MIT-Senseable-City-Lab/flatburn-lte/documentation/content/explore/demo_usb_data.gif

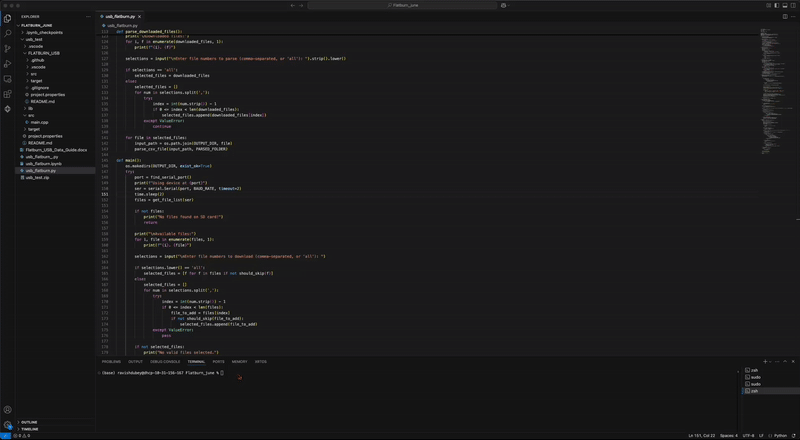
documentation/content/explore/demo_usb_data.gif
