MIT-Senseable-City-Lab/flatburn-lte/hardware/enclosure/step/mechanics/3d_printing/switch radial - R10307RN02Q/MP-05 switch_bottom.stp

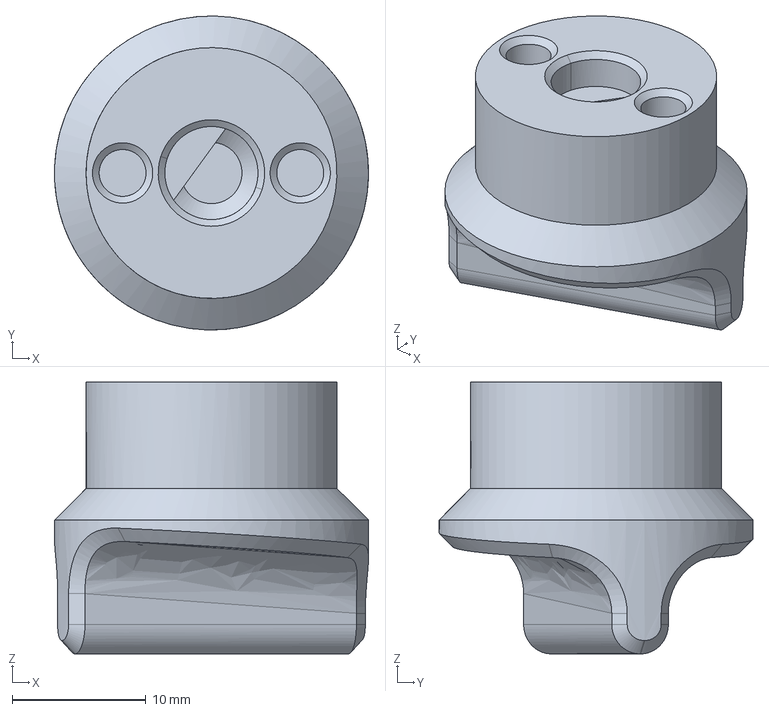
[picture p43: CAD file, 2025-01-15]
hardware/enclosure/step/mechanics/3d_printing/switch radial - R10307RN02Q/MP-05 switch_bottom.stp
23.4 x 23.4 x 20.3 mm
