MIT-Senseable-City-Lab/flatburn-lte/hardware/enclosure/step/mechanics/sealing/MS-02 oring_cord.stp

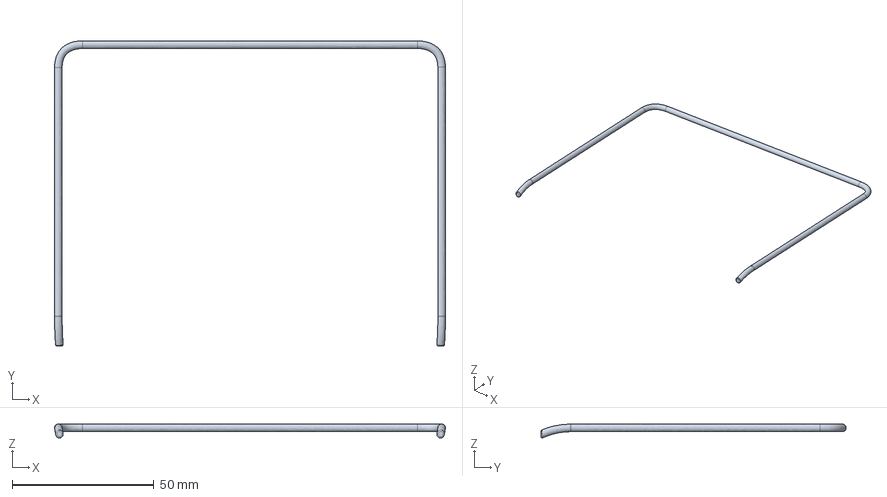
[picture p44: CAD file, 2025-01-15]
hardware/enclosure/step/mechanics/sealing/MS-02 oring_cord.stp
137.8 x 107.6 x 4.94 mm
