MIT-Senseable-City-Lab/flatburn-lte/hardware/enclosure/stl/MP-06 battery_cover.stl

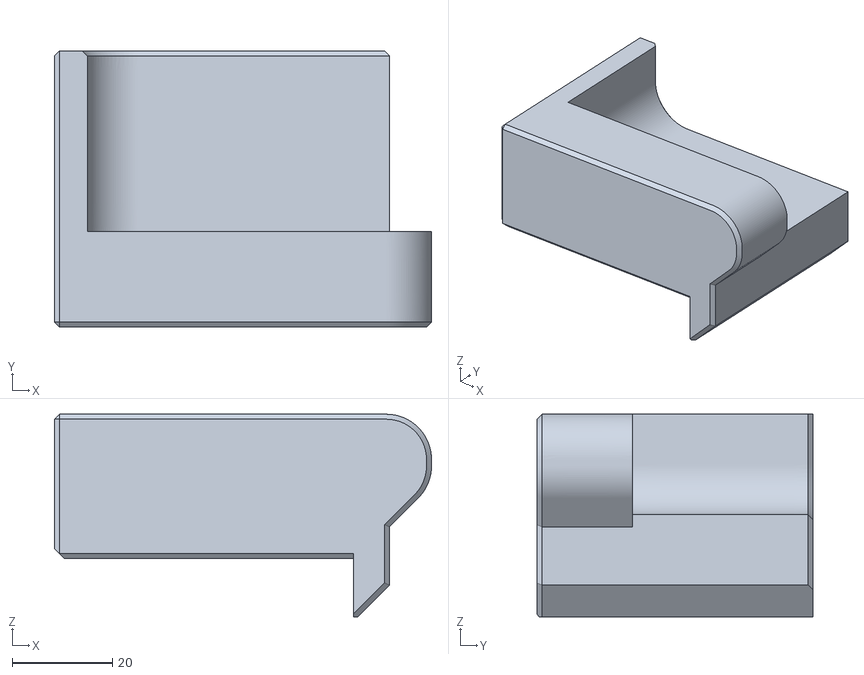
[picture p45: CAD file, 2025-01-15]
hardware/enclosure/stl/MP-06 battery_cover.stl
75.1 x 55.0 x 40.3
