MIT-Senseable-City-Lab/flatburn-lte/hardware/enclosure/bambu/switch_linear_SLW-135987-5A-N-D.3mf

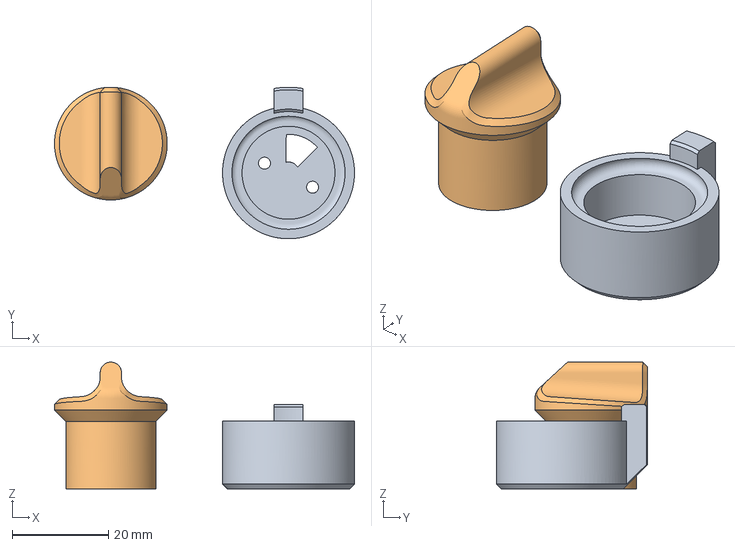
[picture p46: CAD file, 2025-01-20]
hardware/enclosure/bambu/switch_linear_SLW-135987-5A-N-D.3mf
62.4 x 31.5 x 26.4 mm
MP-04 switch_top.stl
MP-05 switch_bottom.stl
