MIT-Senseable-City-Lab/flatburn-lte/hardware/enclosure/step/electronics/switch linear - SLW-135987-5A-N-D.stp

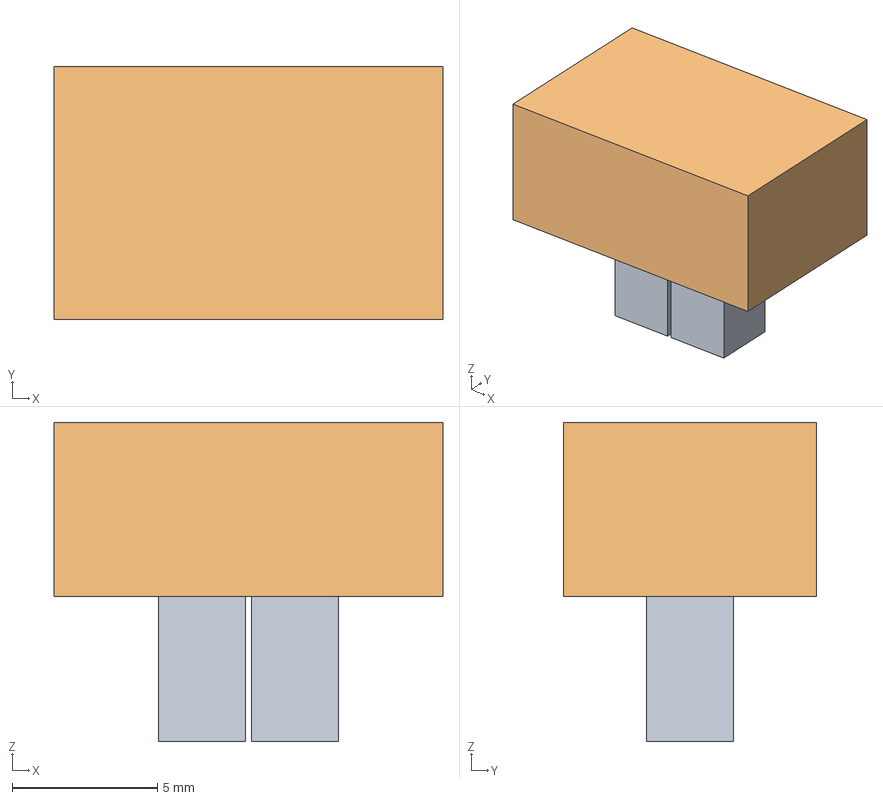
[picture p47: CAD file, 2025-01-16]
hardware/enclosure/step/electronics/switch linear - SLW-135987-5A-N-D.stp
13.4 x 8.70 x 11.0 mm
