MIT-Senseable-City-Lab/flatburn-lte/hardware/enclosure/step/mechanics/fixation/MF-07 spacer_6mm.stp

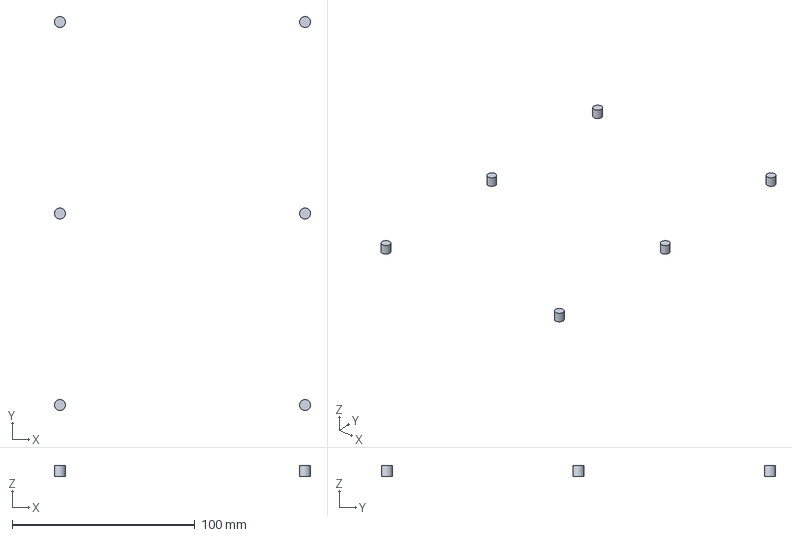
[picture p48: CAD file, 2025-01-15]
hardware/enclosure/step/mechanics/fixation/MF-07 spacer_6mm.stp
140.0 x 215.4 x 6.00 mm
