MIT-Senseable-City-Lab/flatburn-lte/hardware/enclosure/step/electronics/switch linear - FS22AXX.stp

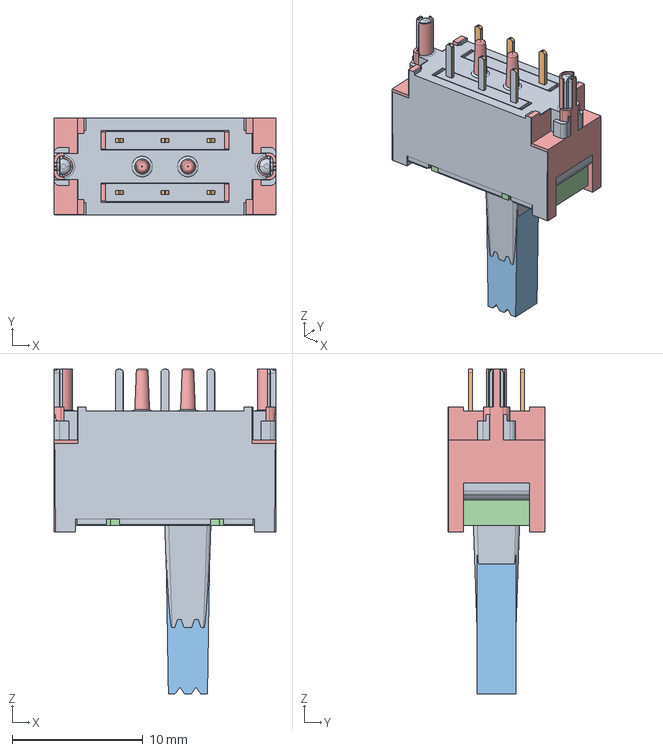
[picture p49: CAD file, 2025-01-16]
hardware/enclosure/step/electronics/switch linear - FS22AXX.stp
17.0 x 7.40 x 24.9 mm
