MIT-Senseable-City-Lab/flatburn-lte/hardware/enclosure/step/mechanics/fixation/MF-02 insert_m2.stp

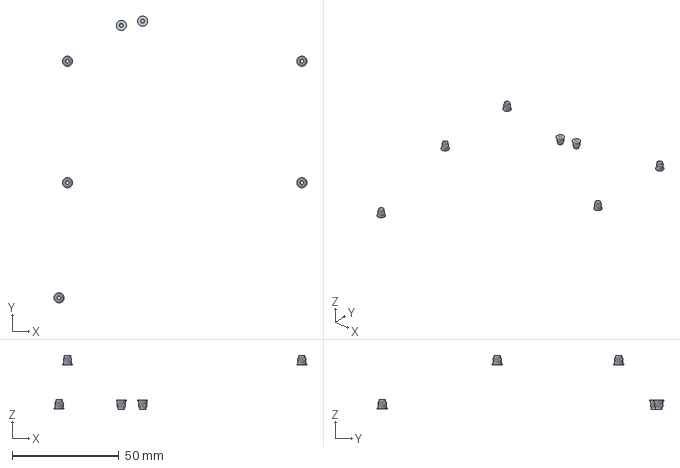
[picture p50: CAD file, 2025-01-15]
hardware/enclosure/step/mechanics/fixation/MF-02 insert_m2.stp
118.7 x 134.6 x 25.5 mm
