MIT-Senseable-City-Lab/flatburn-lte/hardware/enclosure/step/electronics/ES-01 sensor_gas.stp

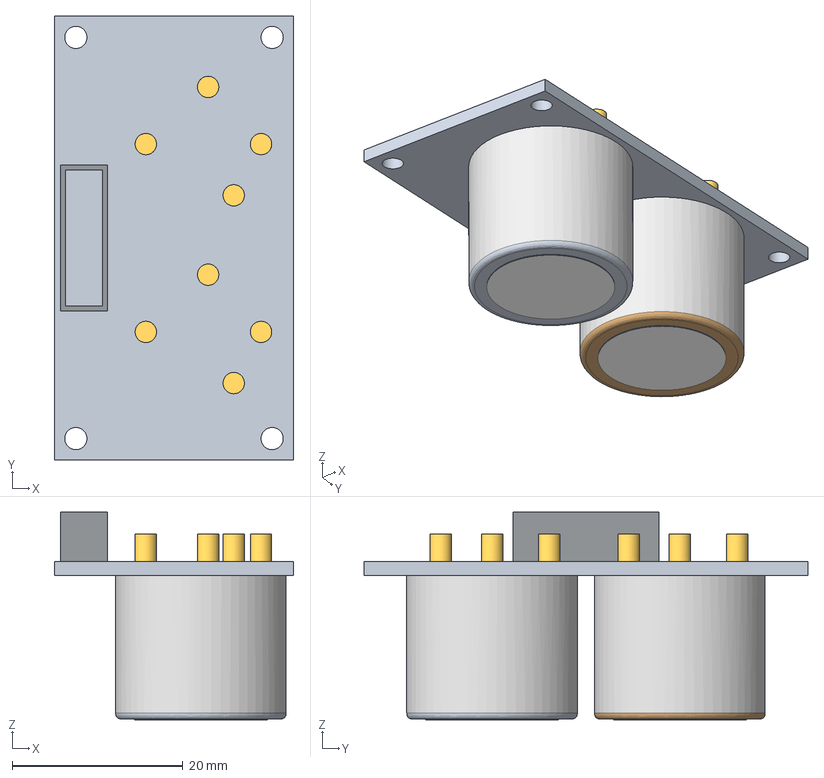
[picture p51: CAD file, 2025-01-15]
hardware/enclosure/step/electronics/ES-01 sensor_gas.stp
28.0 x 52.0 x 24.3 mm
