MIT-Senseable-City-Lab/flatburn-lte/hardware/enclosure/step/electronics/EH-03 90deg_adapter_usb.stp

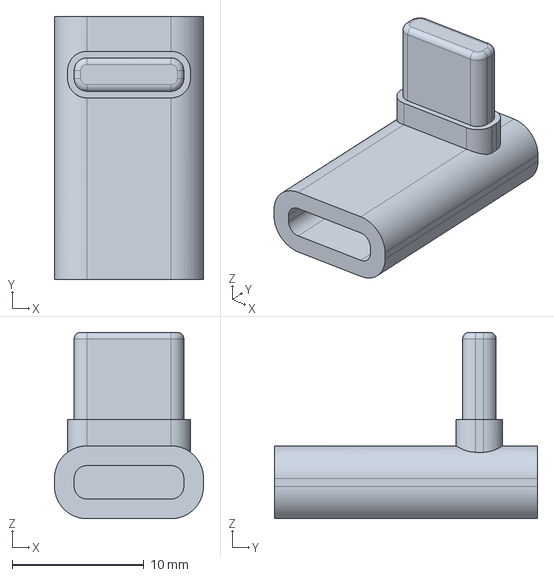
[picture p52: CAD file, 2025-01-15]
hardware/enclosure/step/electronics/EH-03 90deg_adapter_usb.stp
11.3 x 20.0 x 14.2 mm
