MIT-Senseable-City-Lab/flatburn-lte/hardware/enclosure/bambu/switch_linear_FS22AXX.3mf

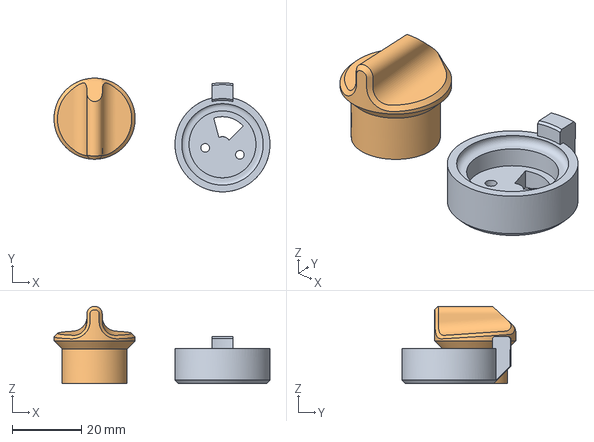
[picture p53: CAD file, 2025-01-15]
hardware/enclosure/bambu/switch_linear_FS22AXX.3mf
62.4 x 32.9 x 22.4 mm
MP-04 switch_top.stl
MP-05 switch_bottom.stl
