MIT-Senseable-City-Lab/flatburn-lte/hardware/enclosure/step/electronics/EP-02 solar_panel.stp

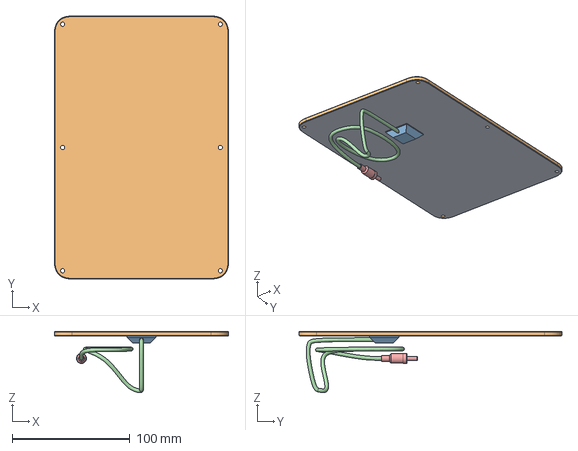
[picture p54: CAD file, 2025-01-15]
hardware/enclosure/step/electronics/EP-02 solar_panel.stp
148.0 x 223.4 x 52.0 mm
