MIT-Senseable-City-Lab/flatburn-lte/hardware/enclosure/step/electronics/EV-01 micro_sd.stp

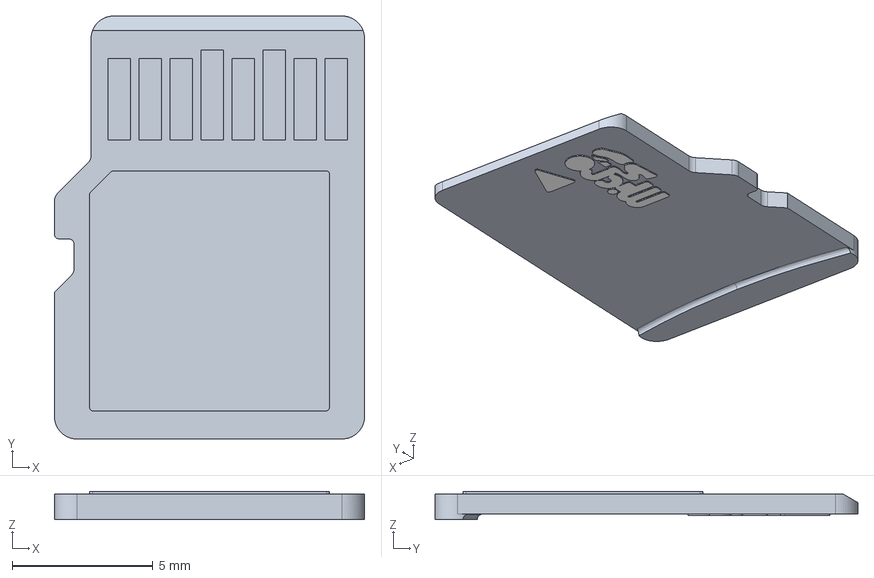
[picture p55: CAD file, 2025-01-15]
hardware/enclosure/step/electronics/EV-01 micro_sd.stp
11.0 x 15.0 x 1.00 mm
