MIT-Senseable-City-Lab/flatburn-lte/hardware/enclosure/step/electronics/ES-02 sensor_particulate.stp

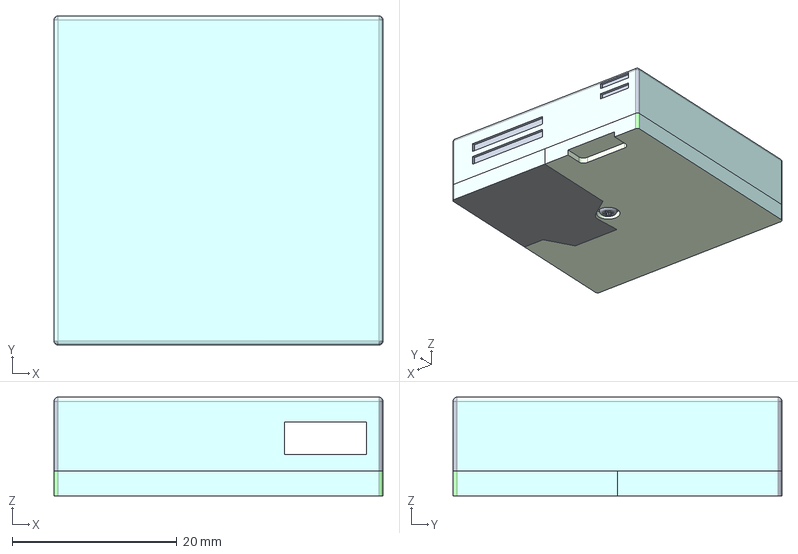
[picture p56: CAD file, 2025-01-15]
hardware/enclosure/step/electronics/ES-02 sensor_particulate.stp
40.0 x 40.0 x 12.0 mm
