MIT-Senseable-City-Lab/flatburn-lte/hardware/enclosure/step/electronics/EP-01 battery.stp

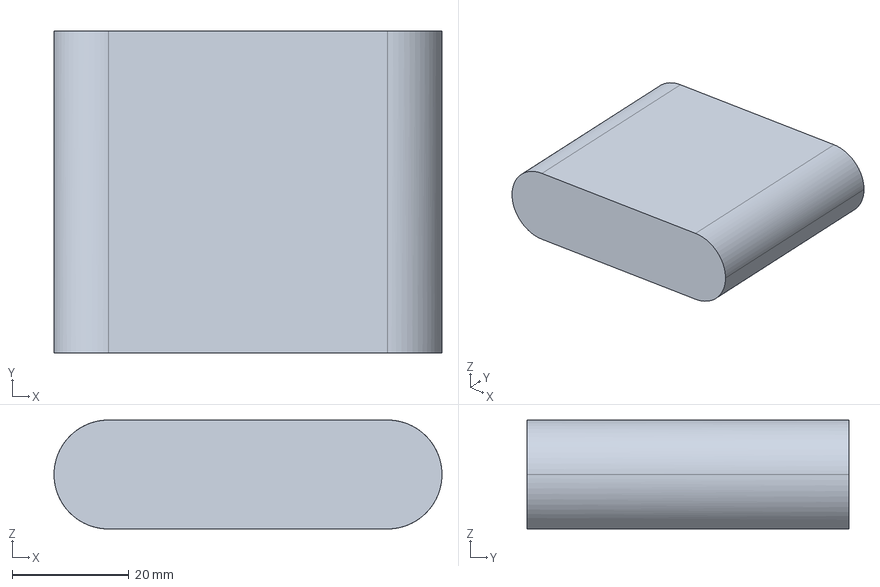
[picture p57: CAD file, 2025-01-15]
hardware/enclosure/step/electronics/EP-01 battery.stp
66.6 x 55.3 x 18.7 mm
