MIT-Senseable-City-Lab/flatburn-lte/hardware/enclosure/step/electronics/EH-04 waterproof_usb.stp

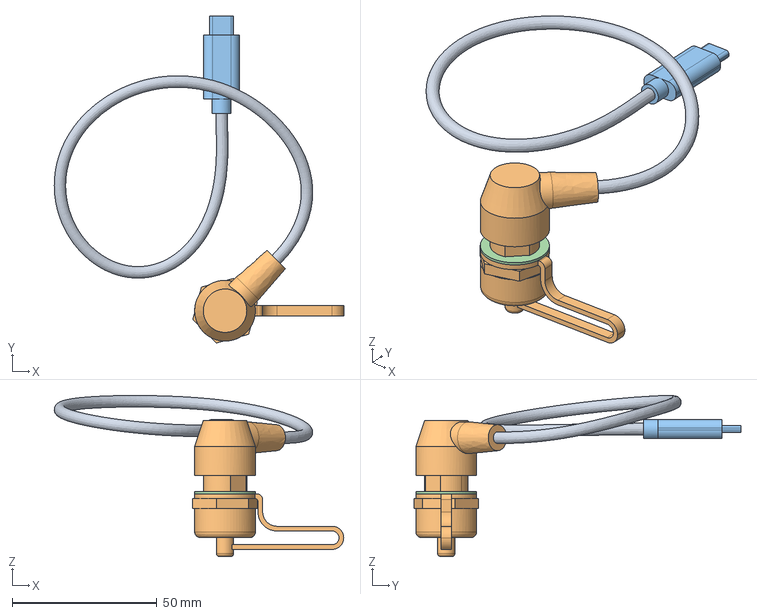
[picture p58: CAD file, 2025-01-15]
hardware/enclosure/step/electronics/EH-04 waterproof_usb.stp
100.0 x 112.9 x 55.6 mm
