MIT-Senseable-City-Lab/flatburn-lte/hardware/electronics/Flatburn_V5.kicad_sch

## KiCad design hardware/electronics/Flatburn_V5.kicad_sch (2025-08-07)

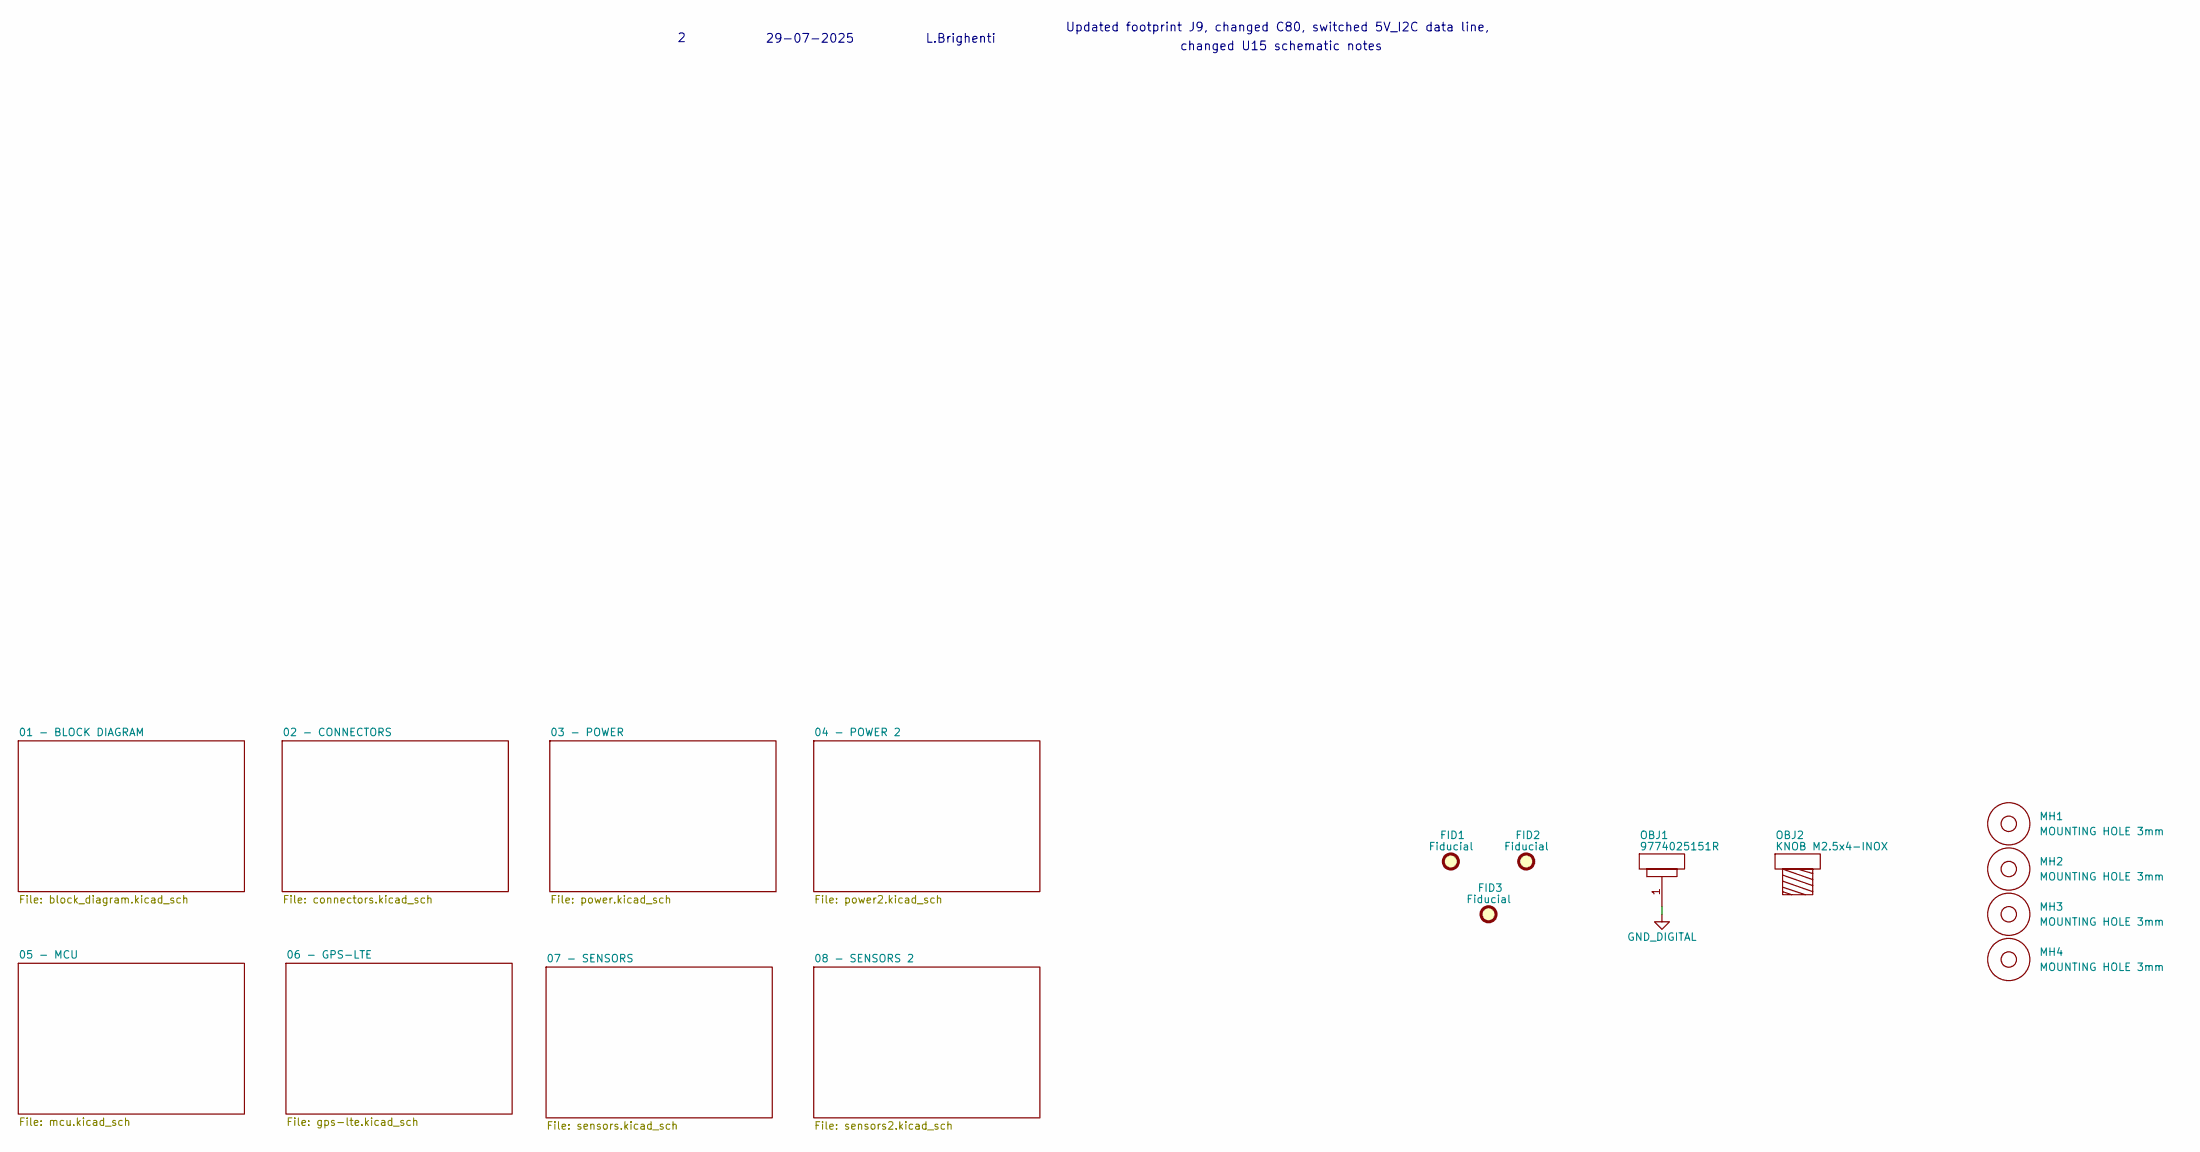
[picture p169: schematic Flatburn_V5.kicad_sch]

Parts:
FID1, FID2, FID3: Fiducial; Fiducial_1mm_Mask3mm
MH1, MH2, MH3, MH4: MOUNTING HOLE 3mm
OBJ1: 9774025151R; SPACER M2.5 - 9774025151R; MPN 9774025151R
OBJ2: KNOB M2.5x4-INOX

Connections:
GND_DIGITAL: OBJ1.1

Notes on the sheet:
L.Brighenti
Updated footprint J9, changed C80, switched 5V_I2C data line,
29-07-2025
changed U15 schematic notes
