MIT-Senseable-City-Lab/flatburn-lte/hardware/electronics/connectors.kicad_sch

## KiCad design hardware/electronics/connectors.kicad_sch (2025-08-07)

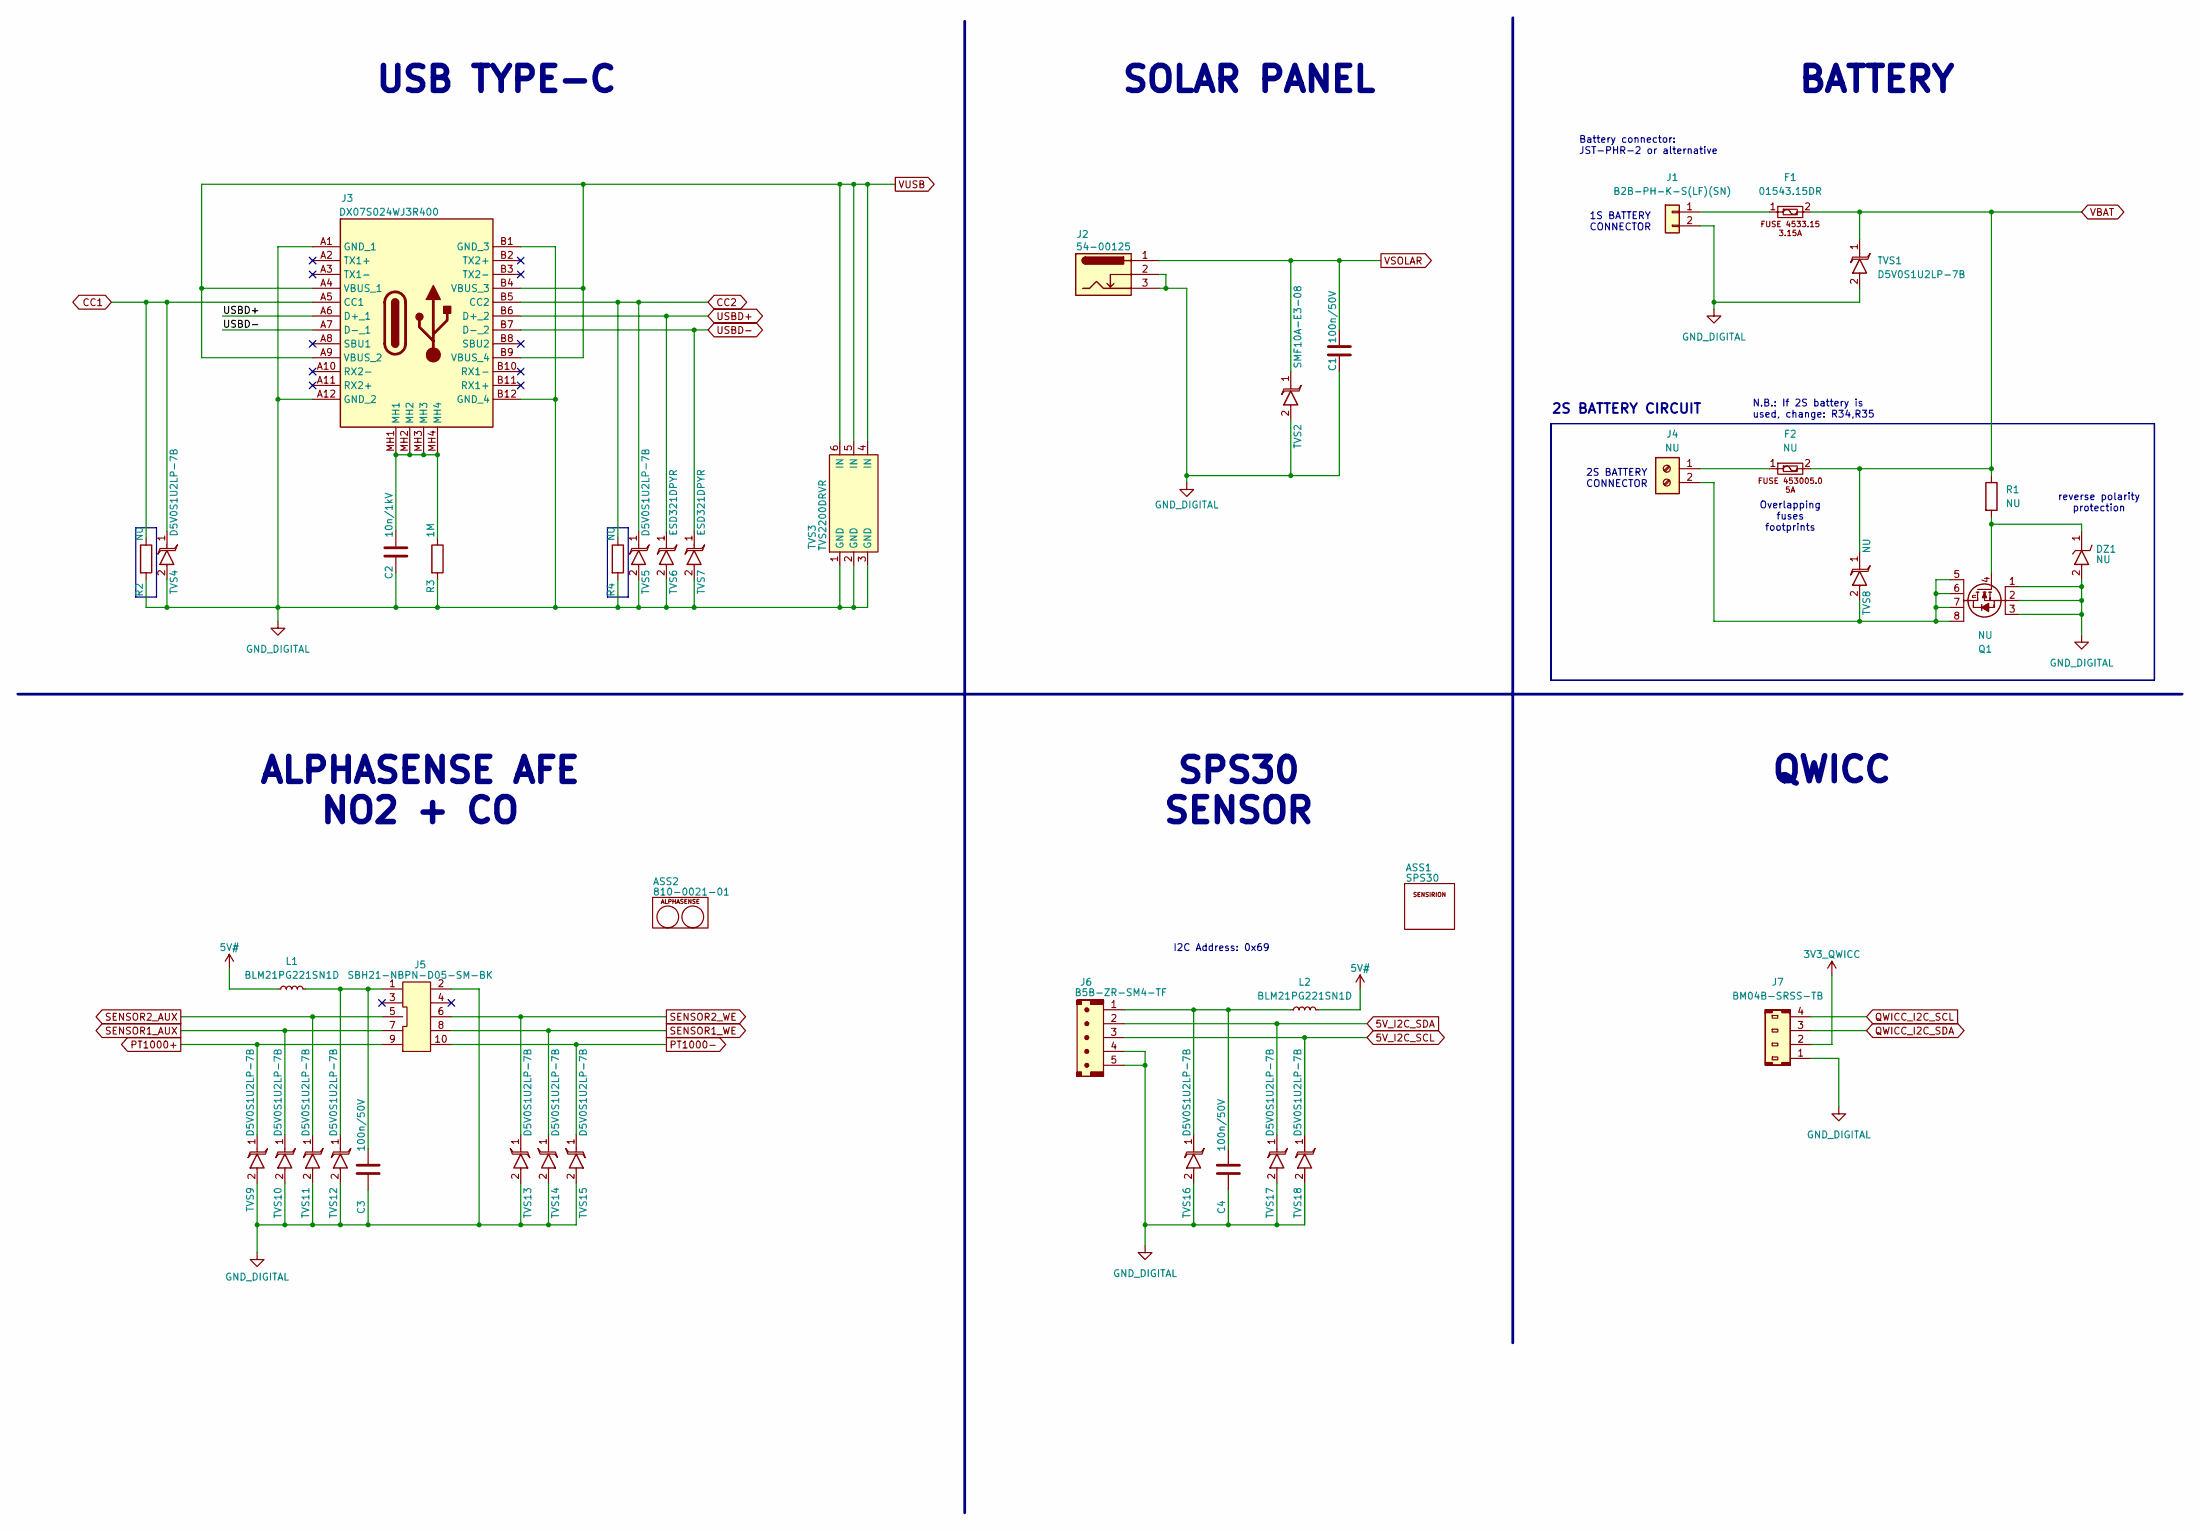
[picture p170: schematic connectors.kicad_sch]

Parts:
ASS1: SPS30; MPN SPS30
ASS2: 810-0021-01; MPN 810-0021-01
C1, C3, C4: 100n/50V; C_0402_1005Metric
C2: 10n/1kV; C_1206_3216Metric
DZ1: NU; D_SOD-523; MPN BZT52C12T-7
F1: 01543.15DR; 154SERIES; MPN 01543.15DR
F2: NU; 154SERIES; MPN 0154005.DR
J1: B2B-PH-K-S(LF)(SN); JST_PH_B2B-PH-K_1x02_P2.00mm_Vertical; MPN B2B-PH-K-S(LF)(SN)
J2: 54-00125; MPN 54-00125
J3: DX07S024WJ3R400; MPN DX07S024WJ3R400
J4: NU; 39543-4302; MPN 39543-4302
J5: SBH21-NBPN-D05-SM-BK; MPN SBH21-NBPN-D05-SM-BK
J6: B5B-ZR-SM4-TF; MPN B5B-ZR-SM4-TF
J7: BM04B-SRSS-TB; BM04B-SRSS_JST; MPN BM04B-SRSS-TB
L1, L2: BLM21PG221SN1D; L_0805_2012Metric; MPN BLM21PG221SN1D
Q1: NU; PowerPAK 121-8; MPN SISH402DN-T1-GE3
R1: NU; R_0402_1005Metric
R2, R4: NU; R_0603_1608Metric; MPN RC0603FR-105K1L
R3: 1M; R_1206_3216Metric
TVS1, TVS4, TVS5, TVS9, TVS10, TVS11, TVS12, TVS13, TVS14, TVS15, TVS16, TVS17, TVS18: D5V0S1U2LP-7B; D5V0S1U2LP7B; MPN M-621-D5V0S1U2LP-7B
TVS2: SMF10A-E3-08; D_SMF; MPN SMF10A-E3-08
TVS3: TVS2200DRVR; SON65P200X200X80-7N; MPN TVS2200DRVR
TVS6, TVS7: ESD321DPYR; X1SON-2; MPN ESD321DPYR
TVS8: NU; D_SMF; MPN SMF10A-E3-08

Connections:
3V3_QWICC: J7.2
5V#: L1.2, L2.1
5V_I2C_SCL: J6.3, TVS18.1
5V_I2C_SDA: J6.2, TVS17.1
CC1: J3.A5 (CC1), R2.1, TVS4.1
CC2: J3.B5 (CC2), R4.1, TVS5.1
GND_DIGITAL: C1.2, C2.2, C3.2, C4.2, DZ1.2, J1.2, J2.2, J2.3, J3.A1 (GND_1), J3.A12 (GND_2), J3.B1 (GND_3), J3.B12 (GND_4), J5.2, J6.4, J6.5, J7.1, Q1.1 (S), Q1.2 (S), Q1.3 (S), R2.2, R3.2, R4.2, TVS1.2, TVS2.2, TVS3.1 (GND), TVS3.2 (GND), TVS3.3 (GND), TVS3.7 (GND), TVS4.2, TVS5.2, TVS6.2, TVS7.2, TVS9.2, TVS10.2, TVS11.2, TVS12.2, TVS13.2, TVS14.2, TVS15.2, TVS16.2, TVS17.2, TVS18.2
unnamed: C2.1, J3.MH1, J3.MH2, J3.MH3, J3.MH4, R3.1
unnamed: C3.1, J5.1, L1.1, TVS12.1
unnamed: C4.1, J6.1, L2.2, TVS16.1
unnamed: DZ1.1, Q1.4 (G), R1.2
unnamed: F1.1, J1.1
unnamed: F2.1, J4.1
unnamed: J4.2, Q1.5 (D), Q1.6 (D), Q1.7 (D), Q1.8 (D), Q1.9 (D), TVS8.2
PT1000+: J5.9, TVS9.1
PT1000-: J5.10, TVS15.1
QWICC_I2C_SCL: J7.4
QWICC_I2C_SDA: J7.3
SENSOR1_AUX: J5.7, TVS10.1
SENSOR1_WE: J5.8, TVS14.1
SENSOR2_AUX: J5.5, TVS11.1
SENSOR2_WE: J5.6, TVS13.1
USBD+: J3.A6 (D+_1), J3.B6 (D+_2), TVS6.1
USBD-: J3.A7 (D-_1), J3.B7 (D-_2), TVS7.1
VBAT: F1.2, F2.2, R1.1, TVS1.1, TVS8.1
VSOLAR: C1.1, J2.1, TVS2.1
VUSB: J3.A4 (VBUS_1), J3.A9 (VBUS_2), J3.B4 (VBUS_3), J3.B9 (VBUS_4), TVS3.4 (IN), TVS3.5 (IN), TVS3.6 (IN)

Notes on the sheet:
SPS30 SENSOR
1S BATTERY CONNECTOR
Overlapping fuses footprints
Battery connector: JST-PHR-2 or alternative
QWICC
reverse polarity protection
BATTERY
SOLAR PANEL
USB TYPE-C
2S BATTERY CONNECTOR
N.B.: If 2S battery is used, change: R34,R35
ALPHASENSE AFE NO2 + CO
2S BATTERY CIRCUIT
I2C Address: 0x69
