MIT-Senseable-City-Lab/flatburn-lte/hardware/electronics/gps-lte.kicad_sch

## KiCad design hardware/electronics/gps-lte.kicad_sch (2025-08-07)

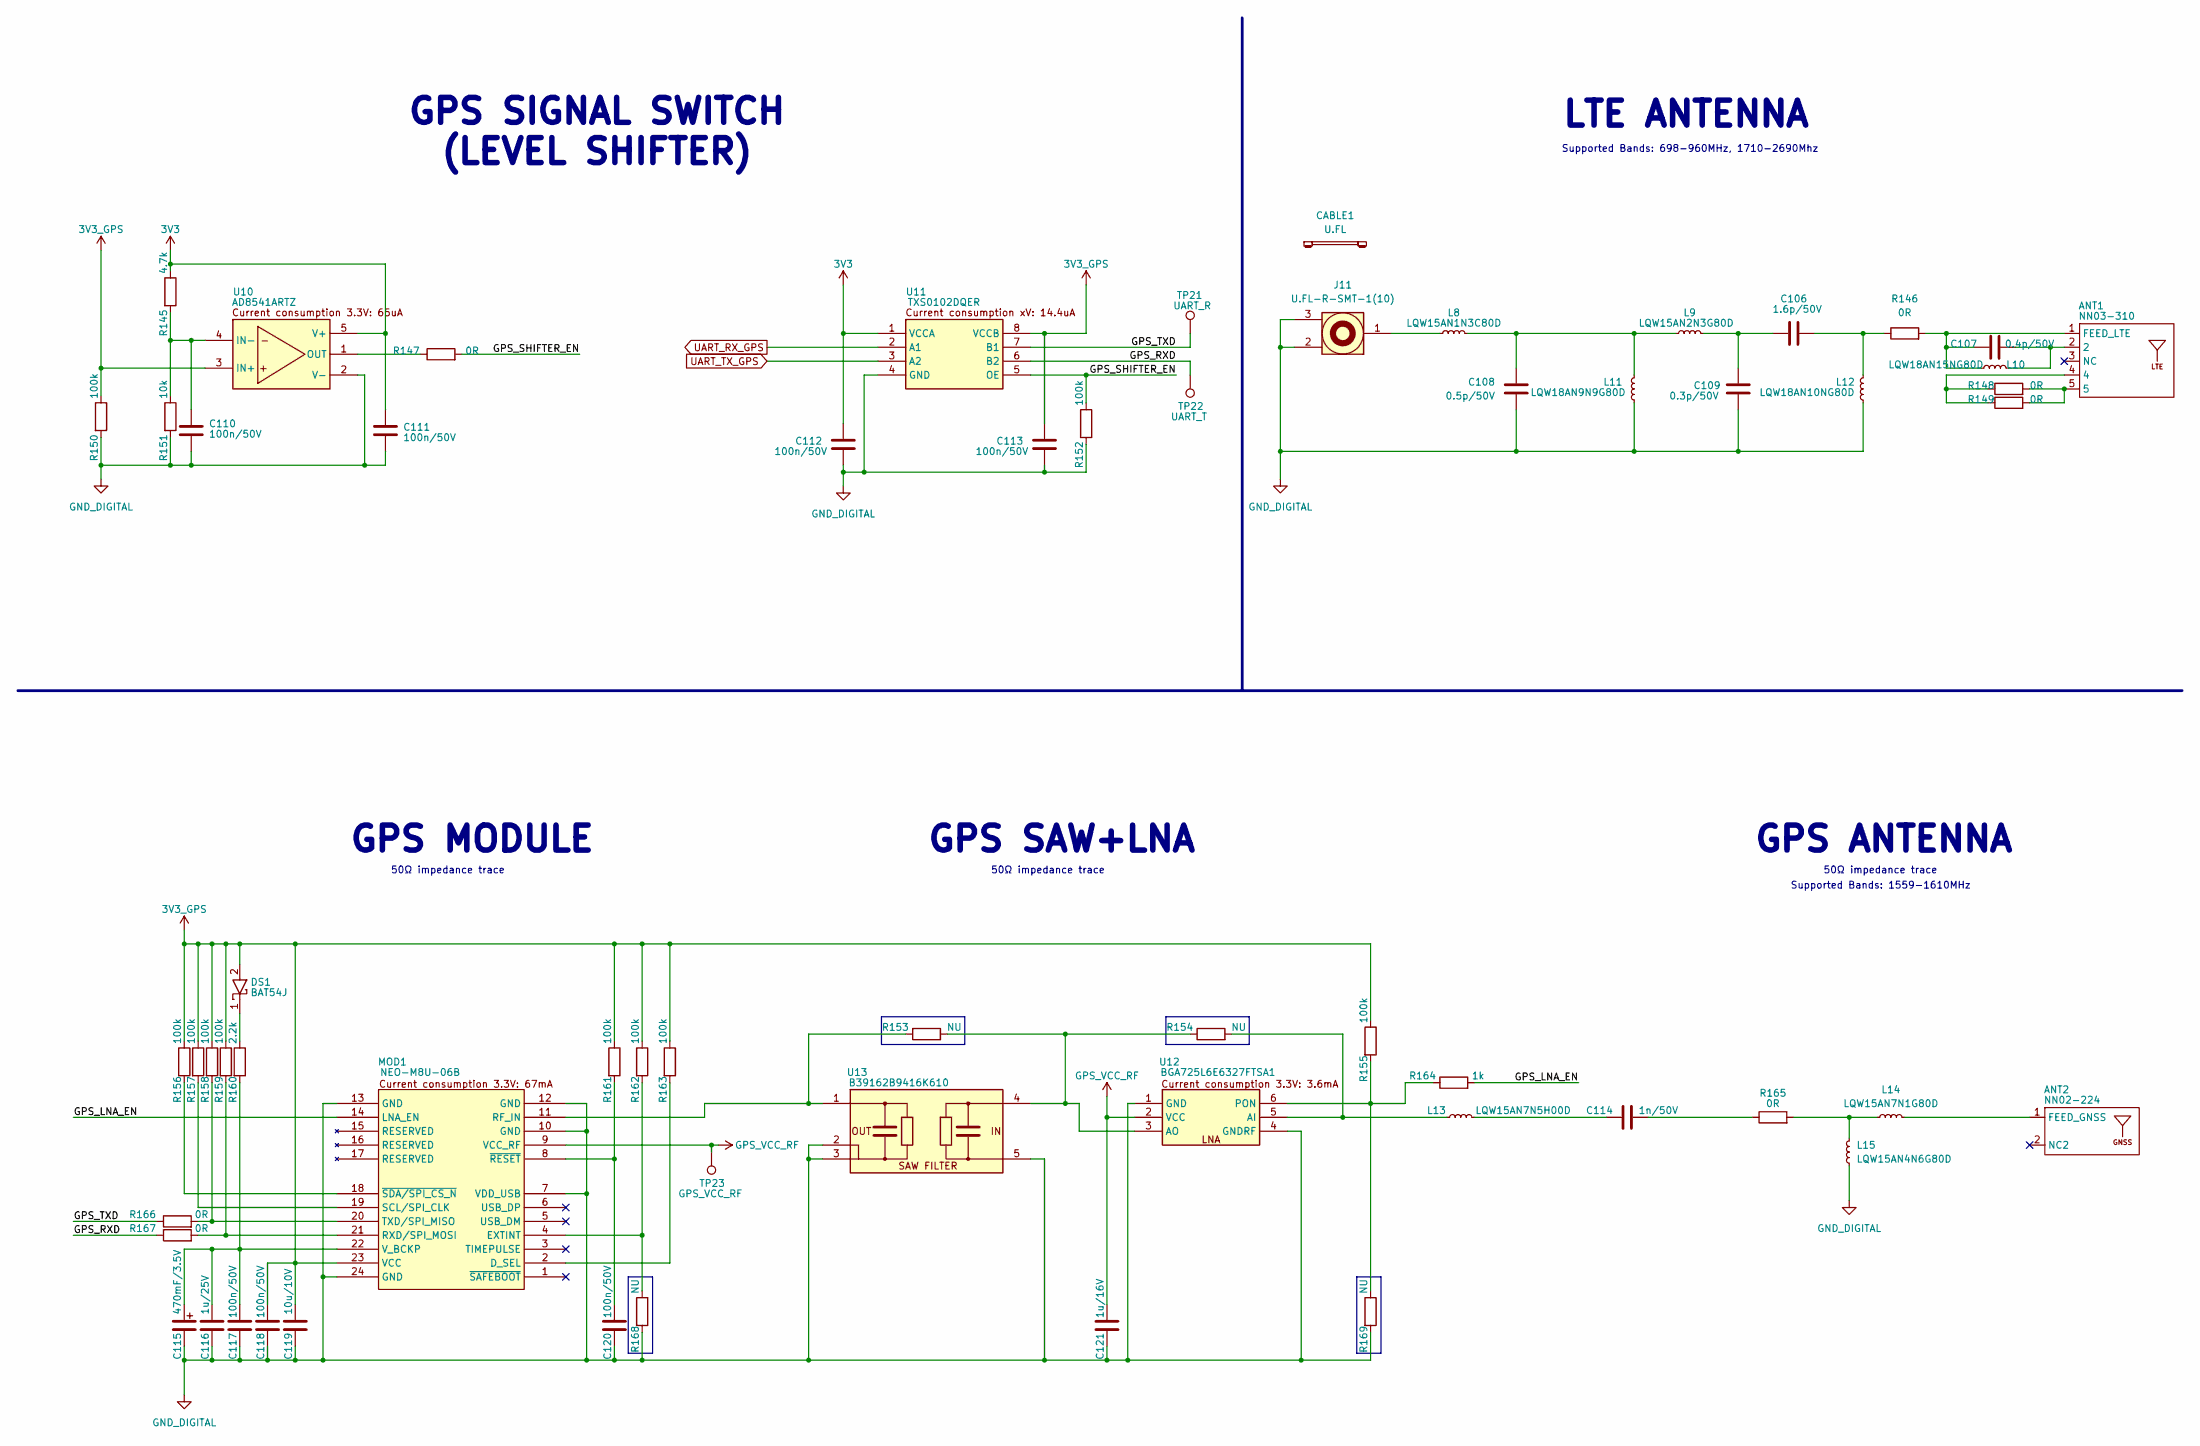
[picture p171: schematic gps-lte.kicad_sch]

Parts:
ANT1: NN03-310; XCVR_NN03-310; MPN NN03-310
ANT2: NN02-224; XCVR_NN02-224; MPN NN02-224
C106: 1.6p/50V; C_0402_1005Metric; MPN GJM1555C1H1R6WB01D
C107: 0.4p/50V; C_0402_1005Metric; MPN GJM1555C1HR40WB01D
C108: 0.5p/50V; C_0402_1005Metric; MPN GJM1555C1HR50WB01D
C109: 0.3p/50V; C_0402_1005Metric; MPN GJM1555C1HR30WB01D
C110, C111, C112, C113, C117, C118, C120: 100n/50V; C_0402_1005Metric
C114: 1n/50V; C_0402_1005Metric
C115: 470mF/3.5V; FCS0V474ZFTBR24_KEM; MPN FCS0V474ZFTBR24
C116: 1u/25V; C_0603_1608Metric; MPN CL10B105KA8NNNC
C119: 10u/10V; C_0603_1608Metric
C121: 1u/16V; C_0402_1005Metric; MPN GRM155C71C105KE11D
CABLE1: U.FL; MPN 2016493-1
DS1: BAT54J; D_SOD-323F; MPN BAT54J,115
J11: U.FL-R-SMT-1(10); MPN U.FL-R-SMT-1(10)
L8: LQW15AN1N3C80D; LQW15AN4N1G80D; MPN LQW15AN1N3C80D
L9: LQW15AN2N3G80D; MPN LQW15AN2N3G80D
L10: LQW18AN15NG80D; LQW18AN7N2G80D; MPN LQW18AN15NG80D
L11: LQW18AN9N9G80D; LQW18AN7N2G80D; MPN LQW18AN9N9G80D
L12: LQW18AN10NG80D; LQW18AN7N2G80D; MPN LQW18AN10NG80D
L13: LQW15AN7N5H00D; MPN LQW15AN7N5H00D
L14: LQW15AN7N1G80D; LQW15AN4N1G80D; MPN LQW15AN7N1G80D
L15: LQW15AN4N6G80D; LQW15AN4N1G80D; MPN LQW15AN4N6G80D
MOD1: NEO-M8U-06B; MOD24_NEO-M8U_UBL; MPN NEO-M8U-06B
R145: 4.7k; R_0402_1005Metric
R146, R148, R149, R165, R166, R167: 0R; R_0402_1005Metric; MPN MCS04020Z0000ZE000
R147: 0R; R_0402_1005Metric; MPN RCS04020000Z0ED
R150, R152, R155, R156, R157, R158, R159, R161, R162, R163: 100k; R_0402_1005Metric
R151: 10k; R_0402_1005Metric
R153, R154: NU; R_0402_1005Metric; MPN RCS04020000Z0ED
R160: 2.2k; R_0402_1005Metric
R164: 1k; R_0402_1005Metric
R168, R169: NU; R_0402_1005Metric
TP21: UART_R; TestPoint_Pad_D1.0mm
TP22: UART_T; TestPoint_Pad_D1.0mm
TP23: GPS_VCC_RF; TestPoint_Pad_D1.0mm
U10: AD8541ARTZ; SOT-23-5; MPN TXS0102DQER
U11: TXS0102DQER; SON35P100X140X40-8N; MPN TXS0102DQER
U12: BGA725L6E6327FTSA1; BGS12SN6E6327XTSA1; MPN BGA725L6E6327FTSA1
U13: B39162B9416K610; MPN B39162B9416K610

Connections:
3V3: C111.1, C112.1, R145.1, U10.5 (V+), U11.1 (VCCA)
3V3_GPS: C113.1, C118.1, C119.1, DS1.2, MOD1.23 (VCC), R150.1, R155.1, R156.1, R157.1, R158.1, R159.1, R161.1, R162.1, R163.1, U10.3 (IN+), U11.8 (VCCB)
GND_DIGITAL: C108.2, C109.2, C110.2, C111.2, C112.2, C113.2, C115.2 (-), C116.2, C117.2, C118.2, C119.2, C120.2, C121.2, J11.2, J11.3, L11.2, L12.2, L15.2, MOD1.7 (VDD_USB), MOD1.10 (GND), MOD1.12 (GND), MOD1.13 (GND), MOD1.24 (GND), R150.2, R151.2, R152.2, R168.2, R169.2, U10.2 (V-), U11.4 (GND), U12.1 (GND), U12.4 (GNDRF), U13.2 (GND1), U13.3 (GND2), U13.5 (GND3)
GPS_LNA_EN: MOD1.14 (LNA_EN), R164.2
GPS_RXD: R167.1, TP22.1, U11.6 (B2)
GPS_SHIFTER_EN: R147.2, R152.1, U11.5 (OE)
GPS_TXD: R166.1, TP21.1, U11.7 (B1)
GPS_VCC_RF: C121.1, MOD1.9 (VCC_RF), TP23.1, U12.2 (VCC)
unnamed: ANT1.1 (FEED_LTE), C107.1, L10.2, R146.2
unnamed: ANT1.2, C107.2, L10.1
unnamed: ANT1.4, R148.1, R149.1
unnamed: ANT1.5, R148.2, R149.2
unnamed: ANT2.1 (FEED_GNSS), L14.1
unnamed: C106.1, C109.1, L9.1
unnamed: C106.2, L12.1, R146.1
unnamed: C108.1, L8.1, L9.2, L11.1
unnamed: C110.1, R145.2, R151.1, U10.4 (IN-)
unnamed: C114.1, L13.1
unnamed: C114.2, R165.1
unnamed: C115.1 (+), C116.1, C117.1, MOD1.22 (V_BCKP), R160.2
unnamed: C120.1, MOD1.8 (~RESET), R161.2
unnamed: DS1.1, R160.1
unnamed: J11.1, L8.2
unnamed: L13.2, R154.2, U12.5 (AI)
unnamed: L14.2, L15.1, R165.2
unnamed: MOD1.2 (D_SEL), R163.2
unnamed: MOD1.4 (EXTINT), R162.2, R168.1
unnamed: MOD1.11 (RF_IN), R153.1, U13.1 (OUT)
unnamed: MOD1.18 (~SDA/SPI_CS_N), R156.2
unnamed: MOD1.19 (SCL/SPI_CLK), R157.2
unnamed: MOD1.20 (TXD/SPI_MISO), R158.2, R166.2
unnamed: MOD1.21 (RXD/SPI_MOSI), R159.2, R167.2
unnamed: R147.1, U10.1 (OUT)
unnamed: R153.2, R154.1, U12.3 (AO), U13.4 (IN)
unnamed: R155.2, R164.1, R169.1, U12.6 (PON)
UART_RX_GPS: U11.2 (A1)
UART_TX_GPS: U11.3 (A2)

Notes on the sheet:
GPS SIGNAL SWITCH (LEVEL SHIFTER)
GPS SAW+LNA
GPS ANTENNA
50Ω impedance trace
LTE ANTENNA
GPS MODULE
Supported Bands: 698-960MHz, 1710-2690Mhz
Supported Bands: 1559-1610MHz
