MIT-Senseable-City-Lab/flatburn-lte/hardware/electronics/mcu.kicad_sch

## KiCad design hardware/electronics/mcu.kicad_sch (2025-08-07)

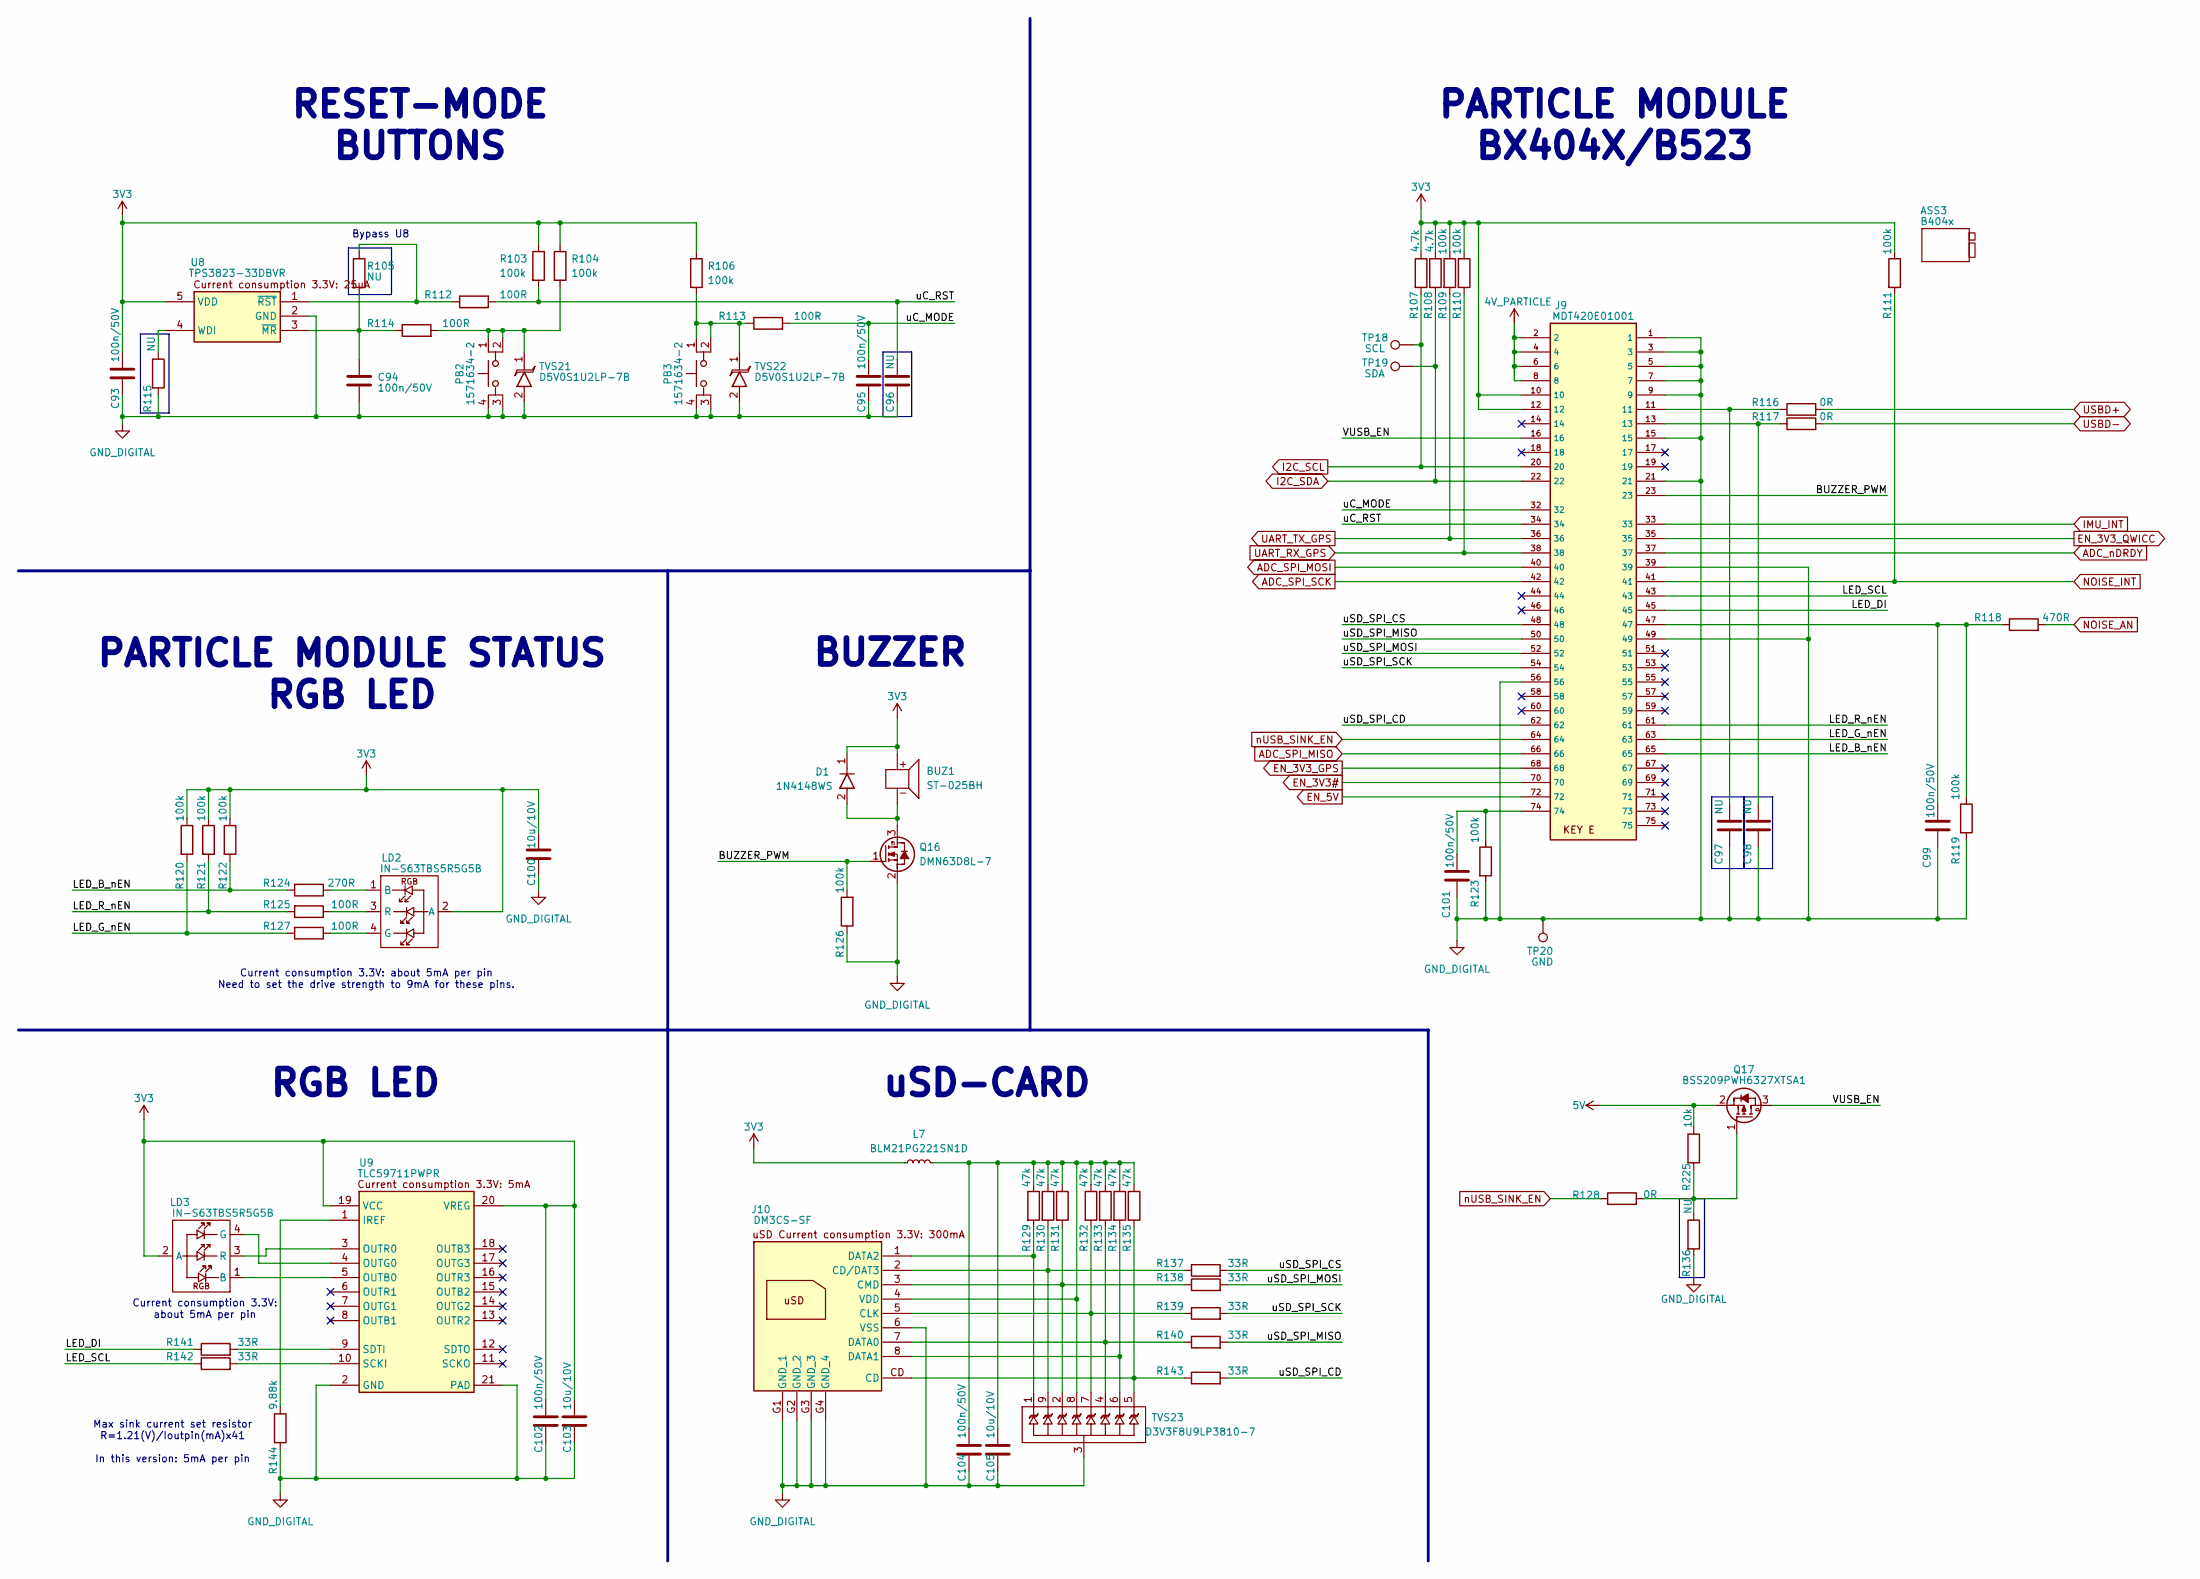
[picture p172: schematic mcu.kicad_sch]

Parts:
ASS3: B404x; PARTICLE B404X-B523; MPN B404x
BUZ1: ST-025BH; ST-025BH_SOB; MPN ST-025BH
C93, C94, C95, C99, C101, C102, C104: 100n/50V; C_0402_1005Metric
C96, C97, C98: NU; C_0402_1005Metric
C100, C103, C105: 10u/10V; C_0603_1608Metric
D1: 1N4148WS; D_SOD-323F; MPN 1N4148WS
J9: MDT420E01001; MPN MDT420E01001
J10: DM3CS-SF; DM3CSSF; MPN DM3CS-SF
L7: BLM21PG221SN1D; L_0805_2012Metric; MPN BLM21PG221SN1D
LD2, LD3: IN-S63TBS5R5G5B; INS63TBS5R5G5B; MPN IN-S63TBS5R5G5B
PB2, PB3: 1571634-2; 15716342; MPN 1571634-2
Q16: DMN63D8L-7; SOT-23; MPN DMN63D8L-7
Q17: BSS209PWH6327XTSA1; SOT-323_SC-70; MPN BSS209PWH6327XTSA1
R103, R104, R106, R109, R110, R111, R119, R120, R121, R122, R123, R126: 100k; R_0402_1005Metric
R105, R136: NU; R_0402_1005Metric; MPN RCS04020000Z0ED
R107, R108: 4.7k; R_0402_1005Metric
R112, R113, R114, R125, R127: 100R; R_0402_1005Metric
R115: NU; R_0402_1005Metric
R116, R117: 0R; R_0402_1005Metric; MPN MCS04020Z0000ZE000
R118: 470R; R_0402_1005Metric
R124: 270R; R_0402_1005Metric; MPN RC0402FR-07270RL
R128: 0R; R_0402_1005Metric; MPN RCS04020000Z0ED
R129, R130, R131, R132, R133, R134, R135: 47k; R_0402_1005Metric
R137, R138, R139, R140, R141, R142, R143: 33R; R_0402_1005Metric
R144: 9.88k; R_0402_1005Metric; MPN RT0402DRD079K88L
R225: 10k; R_0402_1005Metric
TP18: SCL; TestPoint_Pad_D1.0mm
TP19: SDA; TestPoint_Pad_D1.0mm
TP20: GND; TestPoint_Pad_D1.0mm
TVS21, TVS22: D5V0S1U2LP-7B; D5V0S1U2LP7B; MPN M-621-D5V0S1U2LP-7B
TVS23: D3V3F8U9LP3810-7; Diodes_UDFN3810-9_TYPE_B; MPN D3V3F8U9LP3810-7
U8: TPS3823-33DBVR; SOT-23-5; MPN TPS3823-33DBVR
U9: TLC59711PWPR; SOP65P640X120-21N; MPN TLC59711PWPR

Connections:
3V3: BUZ1.2 (+), C93.1, C100.1, C102.1, C103.1, D1.1, J9.10, J9.12, L7.2, LD2.2 (A), LD3.2 (A), R103.1, R104.1, R106.1, R107.1, R108.1, R109.1, R110.1, R111.1, R120.1, R121.1, R122.1, U8.5 (VDD), U9.19 (VCC), U9.20 (VREG)
4V_PARTICLE: J9.2, J9.4, J9.6, J9.8
5V: Q17.2 (S), R225.1
ADC_SPI_MISO: J9.66
ADC_SPI_MOSI: J9.40
ADC_SPI_SCK: J9.42
ADC_nDRDY: J9.37
BUZZER_PWM: J9.23, Q16.1 (G), R126.2
EN_3V3#: J9.70
EN_3V3_GPS: J9.68
EN_3V3_QWICC: J9.35
EN_5V: J9.72
GND_DIGITAL: C93.2, C94.2, C95.2, C96.2, C97.2, C98.2, C99.2, C100.2, C101.2, C102.2, C103.2, C104.2, C105.2, J9.1, J9.3, J9.5, J9.7, J9.9, J9.15, J9.21, J9.39, J9.49, J9.56, J10.6 (VSS), J10.G1 (GND_1), J10.G2 (GND_2), J10.G3 (GND_3), J10.G4 (GND_4), PB2.3, PB2.4, PB3.3, PB3.4, Q16.2 (S), R115.2, R119.2, R123.2, R126.1, R136.2, R144.2, TP20.1, TVS21.2, TVS22.2, TVS23.3, U8.2 (GND), U9.2 (GND), U9.21 (PAD)
I2C_SCL: J9.20, R107.2, TP18.1
I2C_SDA: J9.22, R108.2, TP19.1
IMU_INT: J9.33
LED_B_nEN: J9.65, R122.2, R124.2
LED_DI: J9.45, R141.1
LED_G_nEN: J9.63, R120.2, R127.2
LED_R_nEN: J9.61, R121.2, R125.2
LED_SCL: J9.43, R142.1
NOISE_AN: R118.2
NOISE_INT: J9.41, R111.2
unnamed: BUZ1.3 (-), D1.2, Q16.3 (D)
unnamed: C94.1, R105.2, R114.1, U8.3 (~MR)
unnamed: C97.1, J9.11, R116.1
unnamed: C98.1, J9.13, R117.1
unnamed: C99.1, J9.47, R118.1, R119.1
unnamed: C101.1, J9.74, R123.1
unnamed: C104.1, C105.1, J10.4 (VDD), L7.1, R129.1, R130.1, R131.1, R132.1, R133.1, R134.1, R135.1, TVS23.8
unnamed: J10.1 (DATA2), R129.2, TVS23.1
unnamed: J10.2 (CD/DAT3), R130.2, R137.1, TVS23.9
unnamed: J10.3 (CMD), R131.2, R138.1, TVS23.2
unnamed: J10.5 (CLK), R132.2, R139.1, TVS23.7
unnamed: J10.7 (DATA0), R133.2, R140.1, TVS23.4
unnamed: J10.8 (DATA1), R134.2, TVS23.6
unnamed: J10.CD, R135.2, R143.1, TVS23.5
unnamed: LD2.1 (B), R124.1
unnamed: LD2.3 (R), R125.1
unnamed: LD2.4 (G), R127.1
unnamed: LD3.1 (B), U9.5 (OUTB0)
unnamed: LD3.3 (R), U9.3 (OUTR0)
unnamed: LD3.4 (G), U9.4 (OUTG0)
unnamed: PB2.1, PB2.2, R104.2, R114.2, TVS21.1
unnamed: PB3.1, PB3.2, R106.2, R113.1, TVS22.1
unnamed: Q17.1 (G), R128.2, R136.1, R225.2
unnamed: R105.1, R112.1, U8.1 (~RST)
unnamed: R115.1, U8.4 (WDI)
unnamed: R141.2, U9.9 (SDTI)
unnamed: R142.2, U9.10 (SCKI)
unnamed: R144.1, U9.1 (IREF)
UART_RX_GPS: J9.38, R110.2
UART_TX_GPS: J9.36, R109.2
USBD+: R116.2
USBD-: R117.2
VUSB_EN: J9.16, Q17.3 (D)
nUSB_SINK_EN: J9.64, R128.1
uC_MODE: C95.1, J9.32, R113.2
uC_RST: C96.1, J9.34, R103.2, R112.2
uSD_SPI_CD: J9.62, R143.2
uSD_SPI_CS: J9.48, R137.2
uSD_SPI_MISO: J9.50, R140.2
uSD_SPI_MOSI: J9.52, R138.2
uSD_SPI_SCK: J9.54, R139.2

Notes on the sheet:
Current consumption 3.3V: about 5mA per pin Need to set the drive strength to 9mA for these pins.
BUZZER
uSD-CARD
Bypass U8
Current consumption 3.3V: about 5mA per pin
RESET-MODE BUTTONS
PARTICLE MODULE STATUS RGB LED
RGB LED
Max sink current set resistor R=1.21(V)/Ioutpin(mA)x41 In this version: 5mA per pin
PARTICLE MODULE BX404X/B523
