MIT-Senseable-City-Lab/flatburn-lte/hardware/electronics/power2.kicad_sch

## KiCad design hardware/electronics/power2.kicad_sch (2025-08-07)

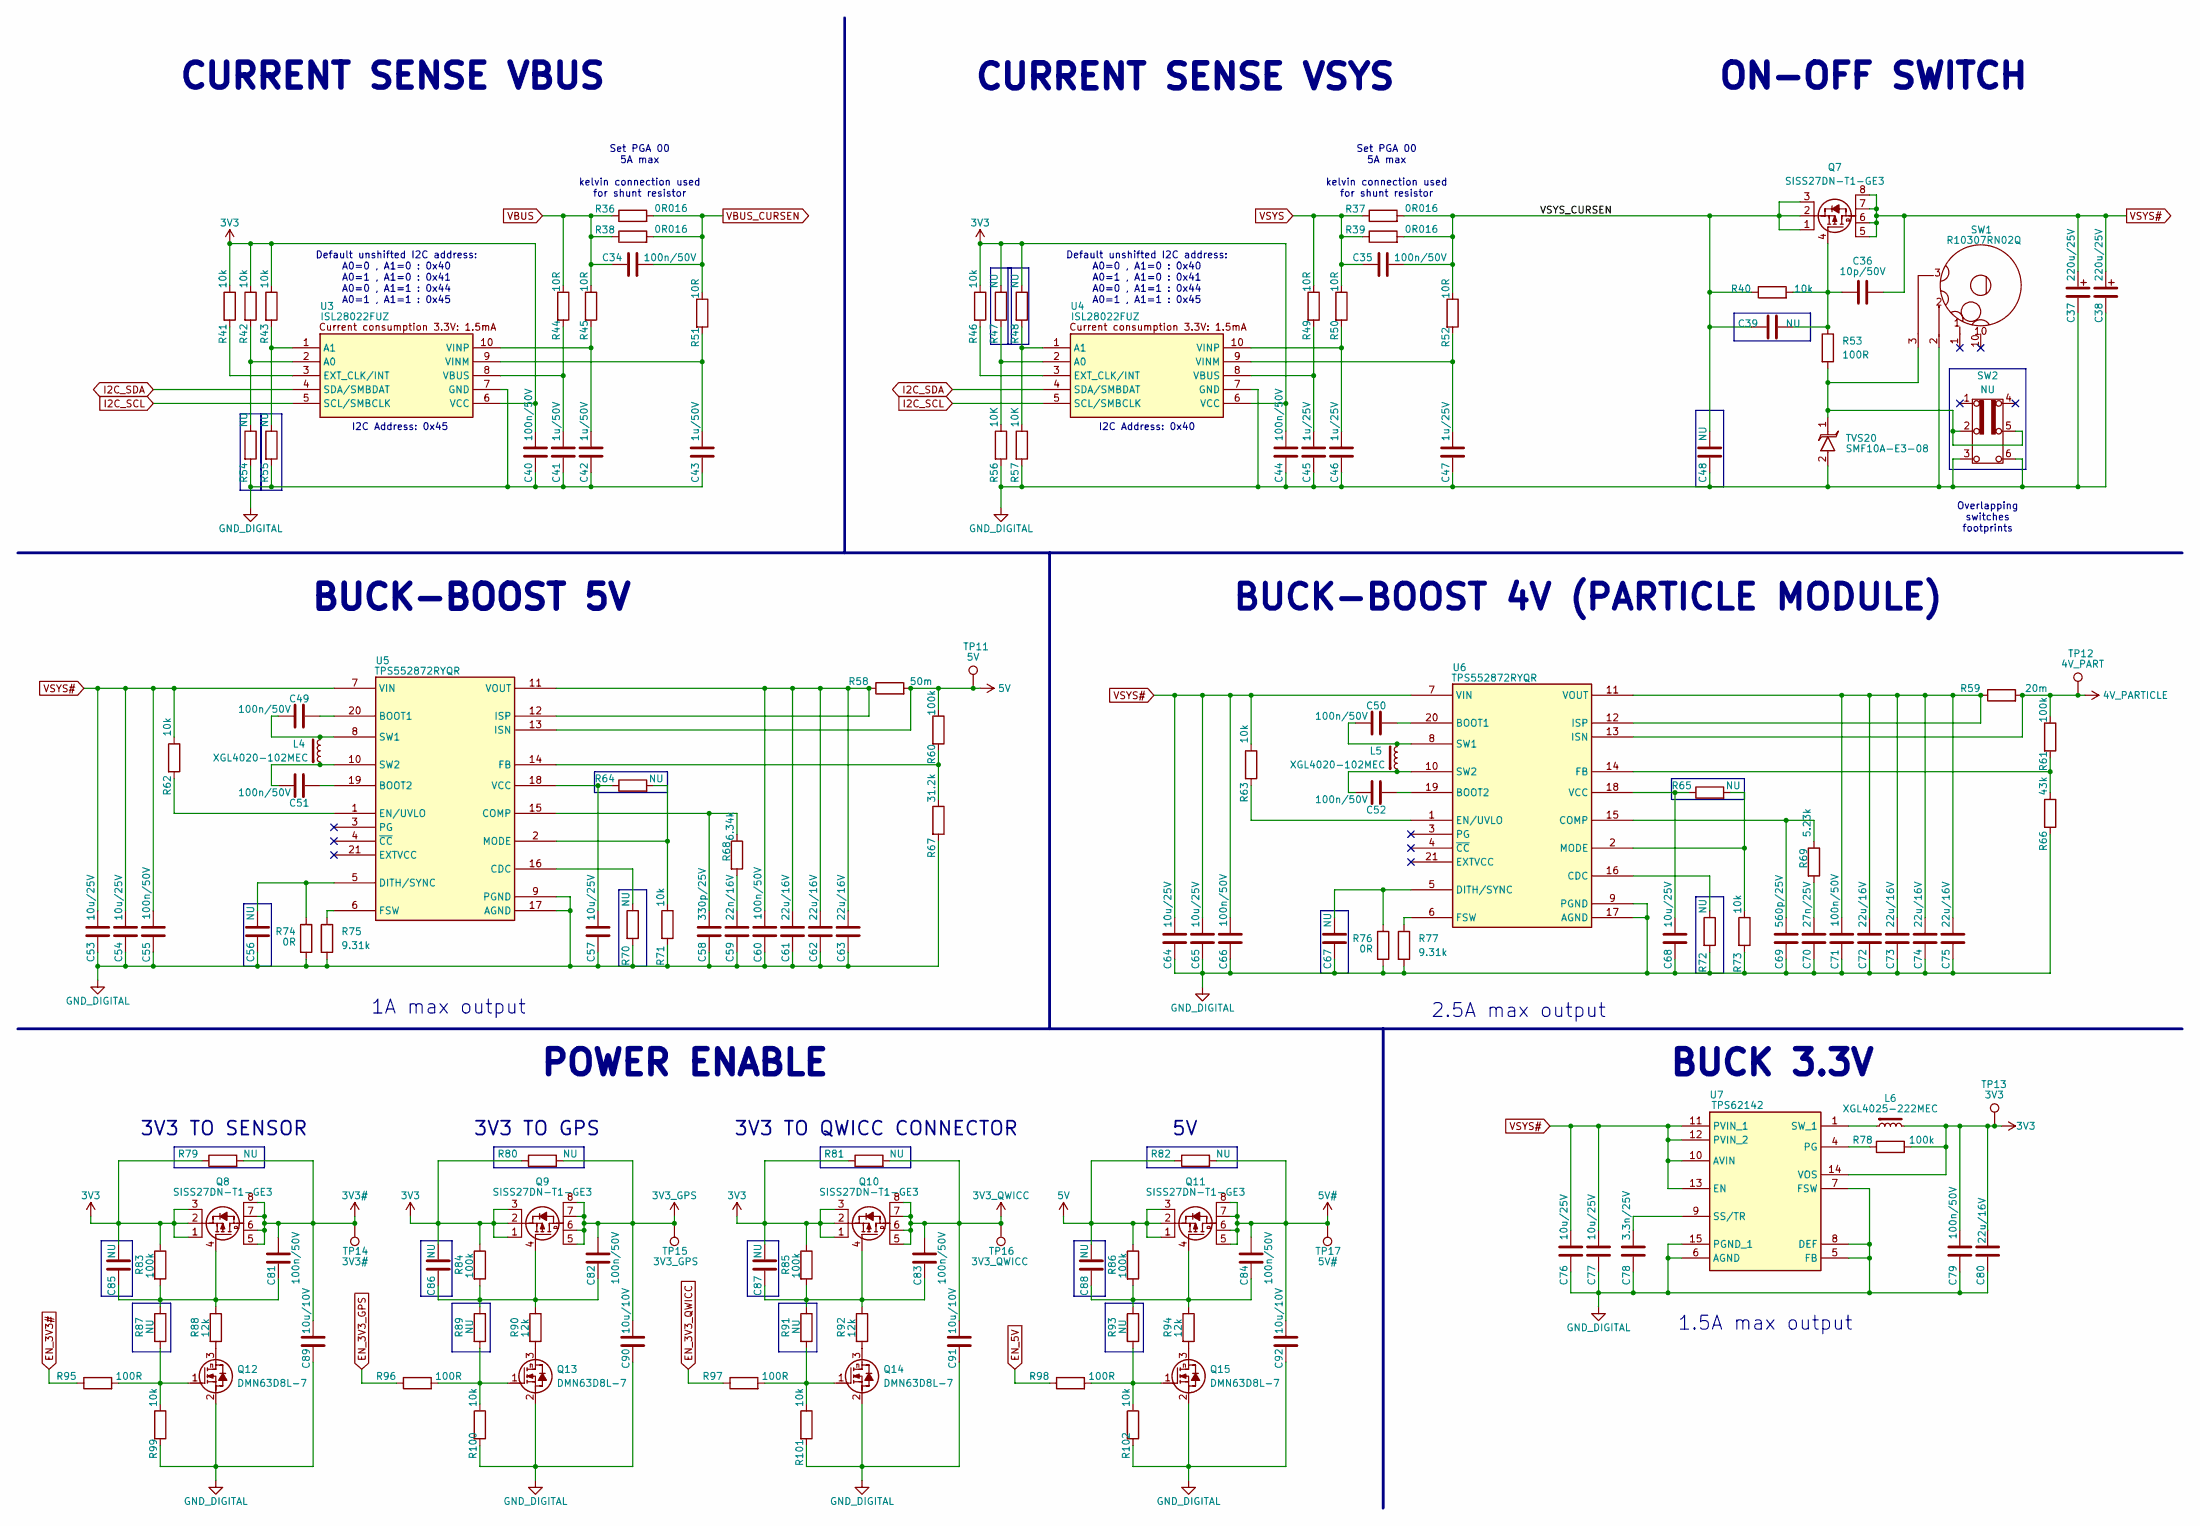
[picture p173: schematic power2.kicad_sch]

Parts:
C34, C35, C40, C44, C49, C50, C51, C52, C55, C60, C66, C71, C79, C81, C82, C83, C84: 100n/50V; C_0402_1005Metric
C36: 10p/50V; C_0402_1005Metric; MPN GCM1555C1H100JA16D
C37, C38: 220u/25V; CP_Elec_6.3x7.7; MPN UCM1E221MCL1GS
C39, C48, C85, C86, C87, C88: NU; C_0402_1005Metric
C41, C42, C43: 1u/50V; C_0805_2012Metric
C45, C46, C47: 1u/25V; C_0603_1608Metric; MPN CL10B105KA8NNNC
C53, C54, C57, C64, C65, C68, C76, C77: 10u/25V; C_0603_1608Metric; MPN GRM188R61E106KA73D
C56, C67: NU; C_0603_1608Metric; MPN GRM188R61E106KA73D
C58: 330p/25V; C_0603_1608Metric; MPN C0603C331J3HACAUTO
C59: 22n/16V; C_0603_1608Metric; MPN 0603YC223J4T2A
C61, C62, C63, C72, C73, C74, C75: 22u/16V; C_0805_2012Metric; MPN GRM21BC81C226ME44L
C69: 560p/25V; C_0603_1608Metric; MPN GRM1885C1E561JA01D
C70: 27n/25V; C_0603_1608Metric; MPN C0603C273J3RACAUTO
C78: 3.3n/25V; C_0402_1005Metric; MPN 885012205047
C80: 22u/16V; C_0603_1608Metric; MPN KGM15CR51C226MT
C89, C90, C91, C92: 10u/10V; C_0603_1608Metric
L4, L5: XGL4020-102MEC; L_Coilcraft_XxL4020; MPN XGL4020-102MEC
L6: XGL4025-222MEC; L_Coilcraft_XxL4020; MPN XGL4025-222MEC
Q7, Q8, Q9, Q10, Q11: SISS27DN-T1-GE3; PowerPAK 121-8; MPN SISS27DN-T1-GE3
Q12, Q13, Q14, Q15: DMN63D8L-7; SOT-23; MPN DMN63D8L-7
R36, R37, R38, R39: 0R016; R_1206_3216Metric; MPN RL1206FR-070R016L
R40, R41, R42, R43, R46, R62, R63, R71, R73, R99, R100, R101, R102: 10k; R_0402_1005Metric
R44, R45, R49, R50, R51, R52: 10R; R_0603_1608Metric
R47, R48, R54, R55, R64, R65, R70, R72: NU; R_0402_1005Metric
R53, R95, R96, R97, R98: 100R; R_0402_1005Metric
R56, R57: 10K; R_0402_1005Metric
R58: 50m; R_0603_1608Metric; MPN PE0603FRF570R05L
R59: 20m; R_0603_1608Metric; MPN CFN0603-FZ-R020ELF
R60, R61, R78, R83, R84, R85, R86: 100k; R_0402_1005Metric
R66: 43k; R_0402_1005Metric; MPN RC0402FR-0743KL
R67: 31.2k; R_0402_1005Metric; MPN RN73H1ETTP3122D25
R68: 6.34k; R_0603_1608Metric; MPN RR0816P-6341-D-78H
R69: 5.23k; R_0603_1608Metric; MPN CPF0603F5K23C1
R74, R76: 0R; R_0402_1005Metric; MPN RCS04020000Z0ED
R75, R77: 9.31k; R_0402_1005Metric; MPN RC0402FR-079K31L
R79, R80, R81, R82: NU; R_1206_3216Metric; MPN RCA12060000ZSEA
R87, R89, R91, R93: NU; R_0402_1005Metric; MPN RCS04020000Z0ED
R88, R90, R92, R94: 12k; R_0402_1005Metric
SW1: R10307RN02Q; MPN R10307RN02Q
SW2: NU; FS22ABP; MPN FS22ABP
TP11: 5V; TestPoint_Pad_D1.0mm
TP12: 4V_PART; TestPoint_Pad_D1.0mm
TP13: 3V3; TestPoint_Pad_D1.0mm
TP14: 3V3#; TestPoint_Pad_D1.0mm
TP15: 3V3_GPS; TestPoint_Pad_D1.0mm
TP16: 3V3_QWICC; TestPoint_Pad_D1.0mm
TP17: 5V#; TestPoint_Pad_D1.0mm
TVS20: SMF10A-E3-08; D_SMF; MPN SMF10A-E3-08
U3, U4: ISL28022FUZ; SOP50P490X110-10N; MPN ISL28022FUZ
U5, U6: TPS552872RYQR; TPS552892QWRYQRQ1; MPN TPS630702RNMR
U7: TPS62142; QFN50P300X300X100-17N-D; MPN TPS62142RGTT

Connections:
3V3: C40.1, C44.1, C79.2, C80.1, C85.2, C86.2, C87.2, L6.1, Q8.1 (S), Q8.2 (S), Q8.3 (S), Q9.1 (S), Q9.2 (S), Q9.3 (S), Q10.1 (S), Q10.2 (S), Q10.3 (S), R41.1, R42.1, R43.1, R46.1, R47.1, R48.1, R78.2, R79.1, R80.1, R81.1, R83.1, R84.1, R85.1, TP13.1, U3.6 (VCC), U4.6 (VCC), U7.14 (VOS)
3V3#: C81.2, C89.1, Q8.5 (D), Q8.6 (D), Q8.7 (D), Q8.8 (D), Q8.9 (D), R79.2, TP14.1
3V3_GPS: C82.2, C90.1, Q9.5 (D), Q9.6 (D), Q9.7 (D), Q9.8 (D), Q9.9 (D), R80.2, TP15.1
3V3_QWICC: C83.2, C91.1, Q10.5 (D), Q10.6 (D), Q10.7 (D), Q10.8 (D), Q10.9 (D), R81.2, TP16.1
4V_PARTICLE: R59.2, R61.1, TP12.1, U6.13 (ISN)
5V: C88.2, Q11.1 (S), Q11.2 (S), Q11.3 (S), R58.2, R60.1, R82.1, R86.1, TP11.1, U5.13 (ISN)
5V#: C84.2, C92.1, Q11.5 (D), Q11.6 (D), Q11.7 (D), Q11.8 (D), Q11.9 (D), R82.2, TP17.1
EN_3V3#: R95.1
EN_3V3_GPS: R96.1
EN_3V3_QWICC: R97.1
EN_5V: R98.1
GND_DIGITAL: C37.2, C38.2, C40.2, C41.2, C42.2, C43.2, C44.2, C45.2, C46.2, C47.2, C48.2, C53.2, C54.2, C55.1, C56.2, C57.2, C58.2, C59.2, C60.1, C61.2, C62.2, C63.2, C64.2, C65.2, C66.1, C67.2, C68.2, C69.2, C70.2, C71.1, C72.2, C73.2, C74.2, C75.2, C76.2, C77.2, C78.2, C79.1, C80.2, C89.2, C90.2, C91.2, C92.2, Q12.2 (S), Q13.2 (S), Q14.2 (S), Q15.2 (S), R54.2, R55.2, R56.2, R57.2, R66.2, R67.2, R70.2, R71.2, R72.2, R73.2, R74.2, R75.2, R76.2, R77.2, R99.2, R100.2, R101.2, R102.2, SW1.2, SW2.3 (B1), SW2.6 (B2), TVS20.2, U3.7 (GND), U4.7 (GND), U5.9 (PGND), U5.17 (AGND), U6.9 (PGND), U6.17 (AGND), U7.5 (FB), U7.6 (AGND), U7.7 (FSW), U7.8 (DEF), U7.15 (PGND_1), U7.16 (PGND_2)
I2C_SCL: U3.5 (SCL/SMBCLK), U4.5 (SCL/SMBCLK)
I2C_SDA: U3.4 (SDA/SMBDAT), U4.4 (SDA/SMBDAT)
unnamed: C36.1, C39.2, Q7.4 (G), R40.2, R53.1
unnamed: C41.1, R44.2, U3.8 (VBUS)
unnamed: C42.1, R45.2, U3.10 (VINP)
unnamed: C43.1, R51.2, U3.9 (VINM)
unnamed: C45.1, R49.2, U4.8 (VBUS)
unnamed: C46.1, R50.2, U4.10 (VINP)
unnamed: C47.1, R52.2, U4.9 (VINM)
unnamed: C49.1, L4.1, U5.8 (SW1)
unnamed: C49.2, U5.20 (BOOT1)
unnamed: C50.1, L5.1, U6.8 (SW1)
unnamed: C50.2, U6.20 (BOOT1)
unnamed: C51.1, L4.2, U5.10 (SW2)
unnamed: C51.2, U5.19 (BOOT2)
unnamed: C52.1, L5.2, U6.10 (SW2)
unnamed: C52.2, U6.19 (BOOT2)
unnamed: C56.1, R74.1, U5.5 (DITH/SYNC)
unnamed: C57.1, R64.1, U5.18 (VCC)
unnamed: C58.1, R68.1, U5.15 (COMP)
unnamed: C59.1, R68.2
unnamed: C60.2, C61.1, C62.1, C63.1, R58.1, U5.11 (VOUT), U5.12 (ISP)
unnamed: C67.1, R76.1, U6.5 (DITH/SYNC)
unnamed: C68.1, R65.1, U6.18 (VCC)
unnamed: C69.1, R69.1, U6.15 (COMP)
unnamed: C70.1, R69.2
unnamed: C71.2, C72.1, C73.1, C74.1, C75.1, R59.1, U6.11 (VOUT), U6.12 (ISP)
unnamed: C78.1, U7.9 (SS/TR)
unnamed: C81.1, C85.1, Q8.4 (G), R83.2, R87.1, R88.1
unnamed: C82.1, C86.1, Q9.4 (G), R84.2, R89.1, R90.1
unnamed: C83.1, C87.1, Q10.4 (G), R85.2, R91.1, R92.1
unnamed: C84.1, C88.1, Q11.4 (G), R86.2, R93.1, R94.1
unnamed: L6.2, U7.1 (SW_1), U7.2 (SW_2), U7.3 (SW_3)
unnamed: Q12.1 (G), R87.2, R95.2, R99.1
unnamed: Q12.3 (D), R88.2
unnamed: Q13.1 (G), R89.2, R96.2, R100.1
unnamed: Q13.3 (D), R90.2
unnamed: Q14.1 (G), R91.2, R97.2, R101.1
unnamed: Q14.3 (D), R92.2
unnamed: Q15.1 (G), R93.2, R98.2, R102.1
unnamed: Q15.3 (D), R94.2
unnamed: R41.2, U3.3 (EXT_CLK/INT)
unnamed: R42.2, R54.1, U3.2 (A0)
unnamed: R43.2, R55.1, U3.1 (A1)
unnamed: R46.2, U4.3 (EXT_CLK/INT)
unnamed: R47.2, R56.1, U4.2 (A0)
unnamed: R48.2, R57.1, U4.1 (A1)
unnamed: R53.2, SW1.3, SW2.2 (COM), SW2.5 (COM), TVS20.1
unnamed: R60.2, R67.1, U5.14 (FB)
unnamed: R61.2, R66.1, U6.14 (FB)
unnamed: R62.2, U5.1 (EN/UVLO)
unnamed: R63.2, U6.1 (EN/UVLO)
unnamed: R64.2, R71.1, U5.2 (MODE)
unnamed: R65.2, R73.1, U6.2 (MODE)
unnamed: R70.1, U5.16 (CDC)
unnamed: R72.1, U6.16 (CDC)
unnamed: R75.1, U5.6 (FSW)
unnamed: R77.1, U6.6 (FSW)
unnamed: R78.1, U7.4 (PG)
VBUS: C34.2, R36.1, R38.1, R44.1, R45.1
VBUS_CURSEN: C34.1, R36.2, R38.2, R51.1
VSYS: C35.2, R37.1, R39.1, R49.1, R50.1
VSYS#: C36.2, C37.1, C38.1, C53.1, C54.1, C55.2, C64.1, C65.1, C66.2, C76.1, C77.1, Q7.5 (D), Q7.6 (D), Q7.7 (D), Q7.8 (D), Q7.9 (D), R62.1, R63.1, U5.7 (VIN), U6.7 (VIN), U7.10 (AVIN), U7.11 (PVIN_1), U7.12 (PVIN_2), U7.13 (EN)
VSYS_CURSEN: C35.1, C39.1, C48.1, Q7.1 (S), Q7.2 (S), Q7.3 (S), R37.2, R39.2, R40.1, R52.1

Notes on the sheet:
I2C Address: 0x40
CURRENT SENSE VBUS
1A max output
1.5A max output
BUCK-BOOST 5V
3V3 TO GPS
POWER ENABLE
Default unshifted I2C address: A0=0 , A1=0 : 0x40 A0=1 , A1=0 : 0x41 A0=0 , A1=1 : 0x44 A0=1 , A1=1 : 0x45
BUCK-BOOST 4V (PARTICLE MODULE)
I2C Address: 0x45
ON-OFF SWITCH
3V3 TO QWICC CONNECTOR
3V3 TO SENSOR
CURRENT SENSE VSYS
Set PGA 00 5A max kelvin connection used for shunt resistor
Overlapping switches footprints
BUCK 3.3V
2.5A max output
