MIT-Senseable-City-Lab/flatburn-lte/hardware/electronics/power.kicad_sch

## KiCad design hardware/electronics/power.kicad_sch (2025-08-07)

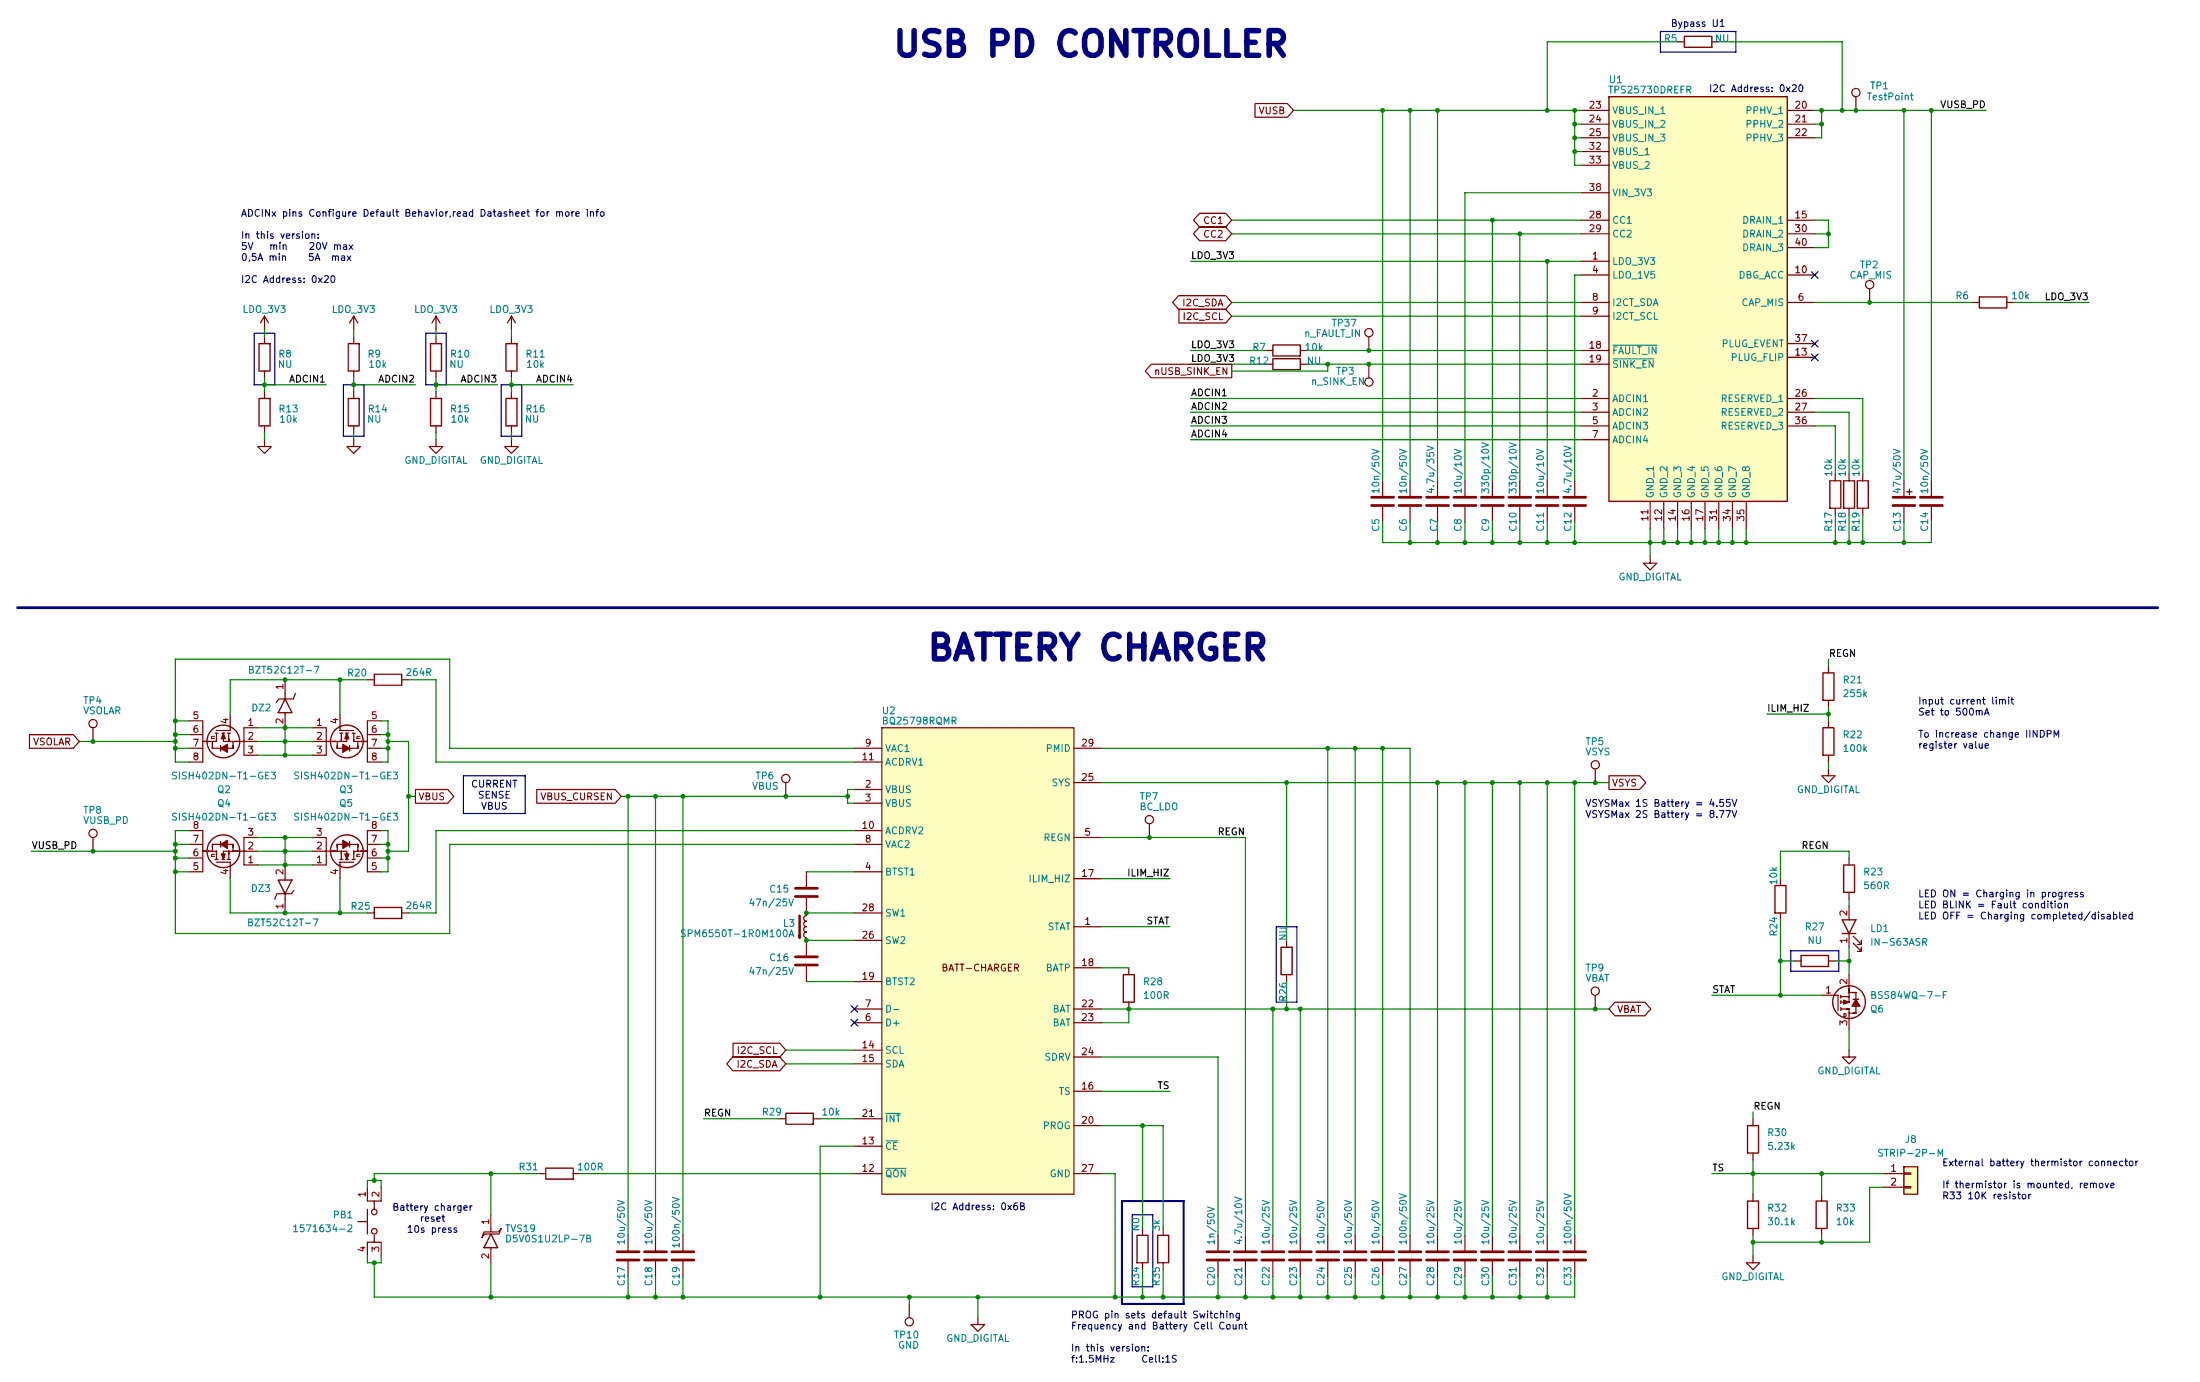
[picture p174: schematic power.kicad_sch]

Parts:
C5, C6, C14: 10n/50V; C_0402_1005Metric
C7: 4.7u/35V; C_0603_1608Metric
C8, C11: 10u/10V; C_0603_1608Metric
C9, C10: 330p/10V; C_0402_1005Metric; MPN C0402C331K8RACTU
C12, C21: 4.7u/10V; C_0603_1608Metric
C13: 47u/50V; CP_Elec_8x10; MPN GXC1H470MCQ1GS
C15, C16: 47n/25V; C_0402_1005Metric
C17, C18, C24, C25, C26: 10u/50V; C_0805_2012Metric; MPN GRM21BR61H106KE43L
C19, C27, C33: 100n/50V; C_0402_1005Metric
C20: 1n/50V; C_0402_1005Metric
C22, C23: 10u/25V; C_0603_1608Metric
C28, C29, C30, C31, C32: 10u/25V; C_0603_1608Metric; MPN GRM188R61E106KA73D
DZ2, DZ3: BZT52C12T-7; D_SOD-523; MPN BZT52C12T-7
J8: STRIP-2P-M; PinHeader_1x02_P2.54mm_Vertical
L3: SPM6550T-1R0M100A; SPM6550; MPN SPM6550T-1R0M100A
LD1: IN-S63ASR; INS63ASR; MPN IN-S63ASR
PB1: 1571634-2; 15716342; MPN 1571634-2
Q2, Q3, Q4, Q5: SISH402DN-T1-GE3; PowerPAK 121-8; MPN SISH402DN-T1-GE3
Q6: BSS84WQ-7-F; SOT-323_SC-70; MPN BSS84WQ-7-F
R5: NU; R_1206_3216Metric; MPN RCA12060000ZSEA
R6, R7, R9, R11, R13, R15, R17, R18, R19, R24, R29, R33: 10k; R_0402_1005Metric
R8, R10, R12, R14, R16: NU; R_0402_1005Metric
R20, R25: 264R; R_0603_1608Metric; MPN CRCW0603294RFKEA
R21: 255k; R_0402_1005Metric; MPN RC0402FR-07255KL
R22: 100k; R_0402_1005Metric
R23: 560R; R_0402_1005Metric
R26: NU; R_0603_1608Metric; MPN RCA06030000ZSEA
R27: NU; R_0402_1005Metric; MPN RCS04020000Z0ED
R28, R31: 100R; R_0402_1005Metric
R30: 5.23k; R_0402_1005Metric
R32: 30.1k; R_0402_1005Metric
R34: NU; R_0603_1608Metric
R35: 3k; R_0603_1608Metric
TP1: TestPoint; TestPoint_Pad_D1.0mm
TP2: CAP_MIS; TestPoint_Pad_D1.0mm
TP3: n_SINK_EN; TestPoint_Pad_D1.0mm
TP4: VSOLAR; TestPoint_Pad_D1.0mm
TP5: VSYS; TestPoint_Pad_D1.0mm
TP6: VBUS; TestPoint_Pad_D1.0mm
TP7: BC_LDO; TestPoint_Pad_D1.0mm
TP8: VUSB_PD; TestPoint_Pad_D1.0mm
TP9: VBAT; TestPoint_Pad_D1.0mm
TP10: GND; TestPoint_Pad_D1.0mm
TP37: n_FAULT_IN; TestPoint_Pad_D1.0mm
TVS19: D5V0S1U2LP-7B; D5V0S1U2LP7B; MPN M-621-D5V0S1U2LP-7B
U1: TPS25730DREFR; MPN TPS25730DREFR
U2: BQ25798RQMR; MPN BQ25798RQMR

Connections:
ADCIN1: R8.1, R13.2, U1.2 (ADCIN1)
ADCIN2: R9.1, R14.2, U1.3 (ADCIN2)
ADCIN3: R10.1, R15.2, U1.5 (ADCIN3)
ADCIN4: R11.1, R16.2, U1.7 (ADCIN4)
CC1: C9.1, U1.28 (CC1)
CC2: C10.1, U1.29 (CC2)
GND_DIGITAL: C5.2, C6.2, C7.2, C8.2, C9.2, C10.2, C11.2, C12.2, C13.2, C14.2, C17.2, C18.2, C19.2, C20.2, C21.2, C22.2, C23.2, C24.2, C25.2, C26.2, C27.2, C28.2, C29.2, C30.2, C31.2, C32.2, C33.2, J8.2, PB1.3, PB1.4, Q6.3 (D), R13.1, R14.1, R15.1, R16.1, R17.2, R18.2, R19.2, R22.2, R32.2, R33.2, R34.2, R35.2, TP10.1, TVS19.2, U1.11 (GND_1), U1.12 (GND_2), U1.14 (GND_3), U1.16 (GND_4), U1.17 (GND_5), U1.31 (GND_6), U1.34 (GND_7), U1.35 (GND_8), U1.39 (GND_9), U1.44 (GND_10), U2.13 (~CE), U2.27 (GND)
I2C_SCL: U1.9 (I2CT_SCL), U2.14 (SCL)
I2C_SDA: U1.8 (I2CT_SDA), U2.15 (SDA)
ILIM_HIZ: R21.2, R22.1, U2.17 (ILIM_HIZ)
LDO_3V3: C11.1, R6.1, R7.1, R8.2, R9.2, R10.2, R11.2, R12.1, U1.1 (LDO_3V3)
unnamed: C8.1, U1.38 (VIN_3V3)
unnamed: C12.1, U1.4 (LDO_1V5)
unnamed: C15.1, U2.4 (BTST1)
unnamed: C15.2, L3.1, U2.28 (SW1)
unnamed: C16.1, L3.2, U2.26 (SW2)
unnamed: C16.2, U2.19 (BTST2)
unnamed: C20.1, U2.24 (SDRV)
unnamed: C24.1, C25.1, C26.1, C27.1, U2.29 (PMID)
unnamed: DZ2.1, Q2.4 (G), Q3.4 (G), R20.1
unnamed: DZ2.2, Q2.1 (S), Q2.2 (S), Q2.3 (S), Q3.1 (S), Q3.2 (S), Q3.3 (S)
unnamed: DZ3.1, Q4.4 (G), Q5.4 (G), R25.1
unnamed: DZ3.2, Q4.1 (S), Q4.2 (S), Q4.3 (S), Q5.1 (S), Q5.2 (S), Q5.3 (S)
unnamed: LD1.1 (K), Q6.2 (S), R27.2
unnamed: LD1.2 (A), R23.2
unnamed: PB1.1, PB1.2, R31.1, TVS19.1
unnamed: R6.2, TP2.1, U1.6 (CAP_MIS)
unnamed: R7.2, TP37.1, U1.18 (~FAULT_IN)
unnamed: R17.1, U1.36 (RESERVED_3)
unnamed: R18.1, U1.27 (RESERVED_2)
unnamed: R19.1, U1.26 (RESERVED_1)
unnamed: R20.2, U2.11 (ACDRV1)
unnamed: R25.2, U2.10 (ACDRV2)
unnamed: R28.1, U2.18 (BATP)
unnamed: R29.2, U2.21 (~INT)
unnamed: R31.2, U2.12 (~QON)
unnamed: R34.1, R35.1, U2.20 (PROG)
unnamed: U1.15 (DRAIN_1), U1.30 (DRAIN_2), U1.40 (DRAIN_3)
REGN: C21.1, R21.1, R23.1, R24.1, R29.1, R30.1, TP7.1, U2.5 (REGN)
STAT: Q6.1 (G), R24.2, R27.1, U2.1 (STAT)
TS: J8.1, R30.2, R32.1, R33.1, U2.16 (TS)
VBAT: C22.1, C23.1, R26.1, R28.2, TP9.1, U2.22 (BAT), U2.23 (BAT)
VBUS: Q3.5 (D), Q3.6 (D), Q3.7 (D), Q3.8 (D), Q3.9 (D), Q5.5 (D), Q5.6 (D), Q5.7 (D), Q5.8 (D), Q5.9 (D)
VBUS_CURSEN: C17.1, C18.1, C19.1, TP6.1, U2.2 (VBUS), U2.3 (VBUS)
VSOLAR: Q2.5 (D), Q2.6 (D), Q2.7 (D), Q2.8 (D), Q2.9 (D), TP4.1, U2.9 (VAC1)
VSYS: C28.1, C29.1, C30.1, C31.1, C32.1, C33.1, R26.2, TP5.1, U2.25 (SYS)
VUSB: C5.1, C6.1, C7.1, R5.1, U1.23 (VBUS_IN_1), U1.24 (VBUS_IN_2), U1.25 (VBUS_IN_3), U1.32 (VBUS_1), U1.33 (VBUS_2), U1.42 (VBUS_IN_4), U1.43 (VBUS_3)
VUSB_PD: C13.1, C14.1, Q4.5 (D), Q4.6 (D), Q4.7 (D), Q4.8 (D), Q4.9 (D), R5.2, TP1.1, TP8.1, U1.20 (PPHV_1), U1.21 (PPHV_2), U1.22 (PPHV_3), U1.41 (PPHV_4), U2.8 (VAC2)
nUSB_SINK_EN: R12.2, TP3.1, U1.19 (~SINK_EN)

Notes on the sheet:
ADCINx pins Configure Default Behavior,read Datasheet for more info In this version: 5V min 20V max 0,5A min 5A max I2C Address: 0x20
CURRENT SENSE VBUS
PROG pin sets default Switching Frequency and Battery Cell Count In this version: f:1.5MHz Cell:1S
I2C Address: 0x6B
Bypass U1
External battery thermistor connector If thermistor is mounted, remove R33 10K resistor
BATTERY CHARGER
Battery charger reset 10s press
VSYSMax 1S Battery = 4.55V VSYSMax 2S Battery = 8.77V
Input current limit Set to 500mA To increase change IINDPM register value
LED ON = Charging in progress LED BLINK = Fault condition LED OFF = Charging completed/disabled
I2C Address: 0x20
USB PD CONTROLLER
