MIT-Senseable-City-Lab/flatburn-lte/hardware/electronics/sensors2.kicad_sch

## KiCad design hardware/electronics/sensors2.kicad_sch (2025-08-07)

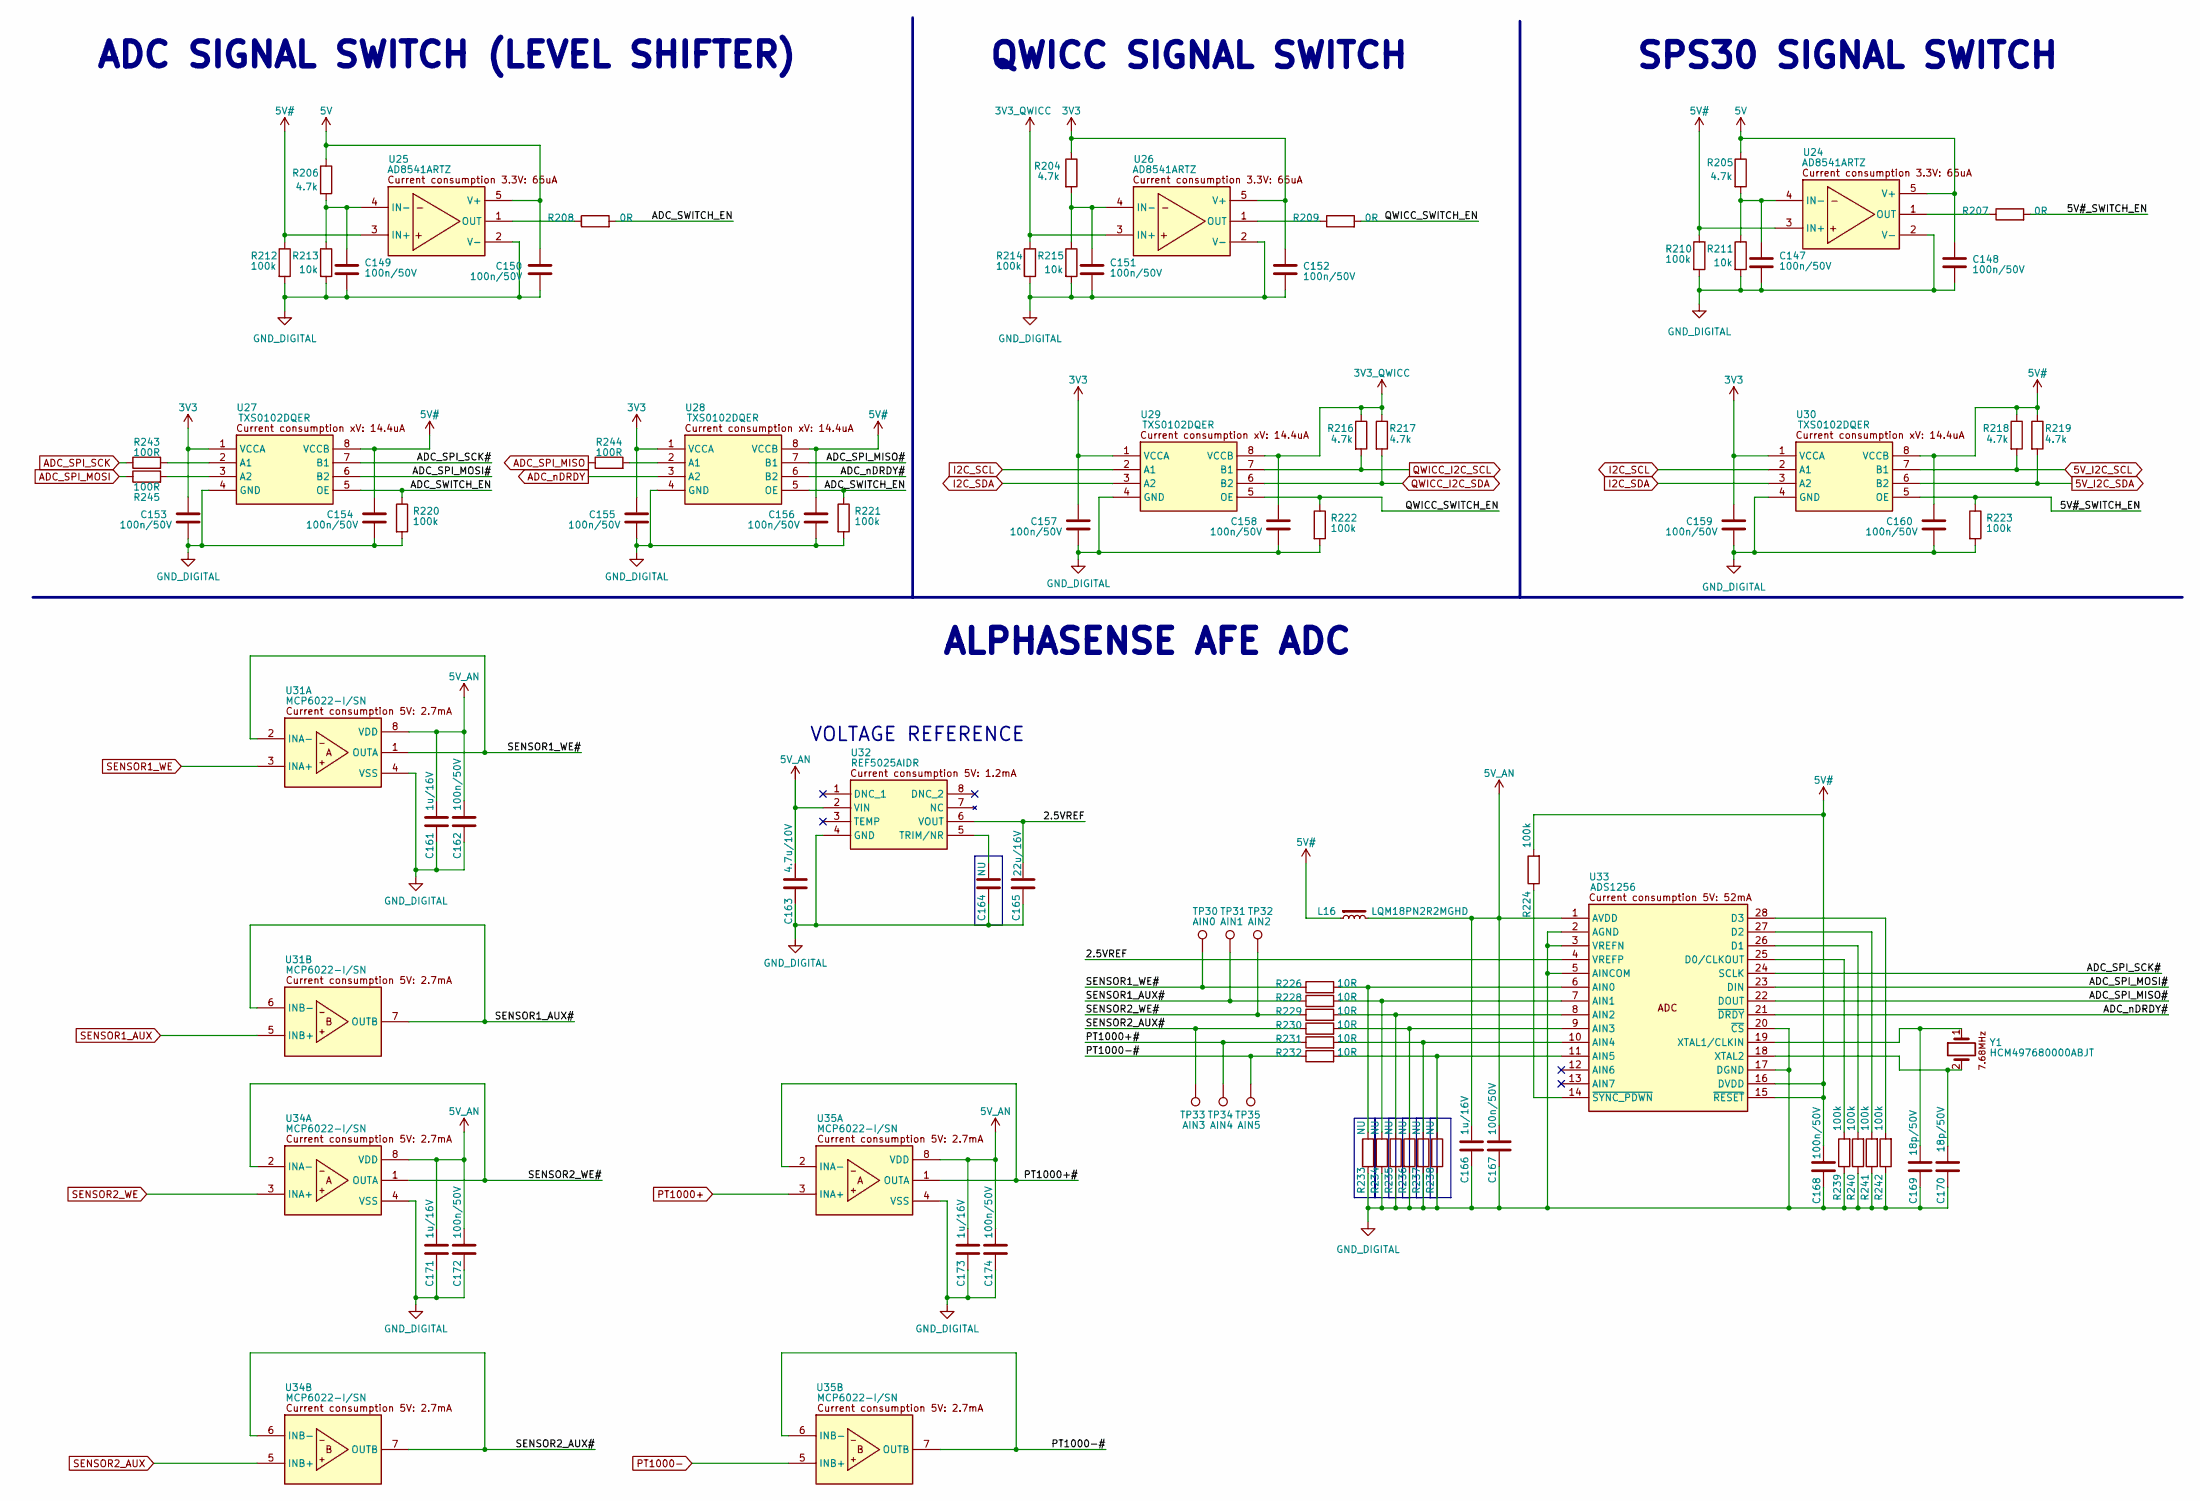
[picture p175: schematic sensors2.kicad_sch]

Parts:
C147, C148, C149, C150, C151, C152, C153, C154, C155, C156, C157, C158, C159, C160, C162, C167, C168, C172, C174: 100n/50V; C_0402_1005Metric
C161, C166, C171, C173: 1u/16V; C_0402_1005Metric; MPN GRM155C71C105KE11D
C163: 4.7u/10V; C_0603_1608Metric
C164: NU; C_0603_1608Metric; MPN CL10B105KA8NNNC
C165: 22u/16V; C_0603_1608Metric; MPN KGM15CR51C226MT
C169, C170: 18p/50V; C_0603_1608Metric; MPN C0603C180J5GAC7411
L16: LQM18PN2R2MGHD; L_0603_1608Metric; MPN LQM18PN2R2MGHD
R204, R205, R206, R216, R217, R218, R219: 4.7k; R_0402_1005Metric
R207, R208, R209: 0R; R_0402_1005Metric; MPN RCS04020000Z0ED
R210, R212, R214, R220, R221, R222, R223, R224, R239, R240, R241, R242: 100k; R_0402_1005Metric
R211, R213, R215: 10k; R_0402_1005Metric
R226, R228, R229, R230, R231, R232: 10R; R_0402_1005Metric; MPN RE0402DRE0710RL
R233, R234, R235, R236, R237, R238: NU; R_0402_1005Metric
R243, R244, R245: 100R; R_0402_1005Metric
TP30: AIN0; TestPoint_Pad_D1.0mm
TP31: AIN1; TestPoint_Pad_D1.0mm
TP32: AIN2; TestPoint_Pad_D1.0mm
TP33: AIN3; TestPoint_Pad_D1.0mm
TP34: AIN4; TestPoint_Pad_D1.0mm
TP35: AIN5; TestPoint_Pad_D1.0mm
U24, U25, U26: AD8541ARTZ; SOT-23-5; MPN TXS0102DQER
U27, U28, U29, U30: TXS0102DQER; SON35P100X140X40-8N; MPN TXS0102DQER
U31, U34, U35: MCP6022-I/SN; SOIC127P600X175-8N; MPN MCP6022-I/SN
U32: REF5025AIDR; SOIC127P600X175-8N; MPN REF5025AIDR
U33: ADS1256; DB28-M; MPN ADS1256IDBR
Y1: HCM497680000ABJT; MPN HCM497680000ABJT

Connections:
2.5VREF: C165.1, U32.6 (VOUT), U33.4 (VREFP)
3V3: C152.1, C153.1, C155.1, C157.1, C159.1, R204.1, U26.5 (V+), U27.1 (VCCA), U28.1 (VCCA), U29.1 (VCCA), U30.1 (VCCA)
3V3_QWICC: C158.1, R214.1, R216.1, R217.1, U26.3 (IN+), U29.8 (VCCB)
5V: C148.1, C150.1, R205.1, R206.1, U24.5 (V+), U25.5 (V+)
5V#: C154.1, C156.1, C160.1, C168.1, L16.2, R210.1, R212.1, R218.1, R219.1, R224.2, U24.3 (IN+), U25.3 (IN+), U27.8 (VCCB), U28.8 (VCCB), U30.8 (VCCB), U33.15 (~RESET), U33.16 (DVDD)
5V#_SWITCH_EN: R207.2, R223.1, U30.5 (OE)
5V_AN: C161.1, C162.1, C163.1, C166.1, C167.1, C171.1, C172.1, C173.1, C174.1, L16.1, U31.8 (VDD), U32.2 (VIN), U33.1 (AVDD), U34.8 (VDD), U35.8 (VDD)
5V_I2C_SCL: R218.2, U30.7 (B1)
5V_I2C_SDA: R219.2, U30.6 (B2)
ADC_SPI_MISO: R244.1
ADC_SPI_MISO#: U28.7 (B1), U33.22 (DOUT)
ADC_SPI_MOSI: R245.1
ADC_SPI_MOSI#: U27.6 (B2), U33.23 (DIN)
ADC_SPI_SCK: R243.1
ADC_SPI_SCK#: U27.7 (B1), U33.24 (SCLK)
ADC_SWITCH_EN: R208.2, R220.1, R221.1, U27.5 (OE), U28.5 (OE)
ADC_nDRDY: U28.3 (A2)
ADC_nDRDY#: U28.6 (B2), U33.21 (~DRDY)
GND_DIGITAL: C147.2, C148.2, C149.2, C150.2, C151.2, C152.2, C153.2, C154.2, C155.2, C156.2, C157.2, C158.2, C159.2, C160.2, C161.2, C162.2, C163.2, C164.2, C165.2, C166.2, C167.2, C168.2, C169.2, C170.2, C171.2, C172.2, C173.2, C174.2, R210.2, R211.2, R212.2, R213.2, R214.2, R215.2, R220.2, R221.2, R222.2, R223.2, R233.2, R234.2, R235.2, R236.2, R237.2, R238.2, R239.1, R240.1, R241.1, R242.1, U24.2 (V-), U25.2 (V-), U26.2 (V-), U27.4 (GND), U28.4 (GND), U29.4 (GND), U30.4 (GND), U31.4 (VSS), U32.4 (GND), U33.2 (AGND), U33.3 (VREFN), U33.5 (AINCOM), U33.17 (DGND), U33.20 (~CS), U34.4 (VSS), U35.4 (VSS)
I2C_SCL: U29.2 (A1), U30.2 (A1)
I2C_SDA: U29.3 (A2), U30.3 (A2)
unnamed: C147.1, R205.2, R211.1, U24.4 (IN-)
unnamed: C149.1, R206.2, R213.1, U25.4 (IN-)
unnamed: C151.1, R204.2, R215.1, U26.4 (IN-)
unnamed: C164.1, U32.5 (TRIM/NR)
unnamed: C169.1, U33.19 (XTAL1/CLKIN), Y1.1
unnamed: C170.1, U33.18 (XTAL2), Y1.2
unnamed: R207.1, U24.1 (OUT)
unnamed: R208.1, U25.1 (OUT)
unnamed: R209.1, U26.1 (OUT)
unnamed: R224.1, U33.14 (~SYNC_PDWN)
unnamed: R226.2, R233.1, U33.6 (AIN0)
unnamed: R228.2, R234.1, U33.7 (AIN1)
unnamed: R229.2, R235.1, U33.8 (AIN2)
unnamed: R230.2, R236.1, U33.9 (AIN3)
unnamed: R231.2, R237.1, U33.10 (AIN4)
unnamed: R232.2, R238.1, U33.11 (AIN5)
unnamed: R239.2, U33.25 (D0/CLKOUT)
unnamed: R240.2, U33.26 (D1)
unnamed: R241.2, U33.27 (D2)
unnamed: R242.2, U33.28 (D3)
unnamed: R243.2, U27.2 (A1)
unnamed: R244.2, U28.2 (A1)
unnamed: R245.2, U27.3 (A2)
PT1000+: U35.3 (INA+)
PT1000+#: R231.1, TP34.1, U35.1 (OUTA), U35.2 (INA-)
PT1000-: U35.5 (INB+)
PT1000-#: R232.1, TP35.1, U35.6 (INB-), U35.7 (OUTB)
QWICC_I2C_SCL: R216.2, U29.7 (B1)
QWICC_I2C_SDA: R217.2, U29.6 (B2)
QWICC_SWITCH_EN: R209.2, R222.1, U29.5 (OE)
SENSOR1_AUX: U31.5 (INB+)
SENSOR1_AUX#: R228.1, TP31.1, U31.6 (INB-), U31.7 (OUTB)
SENSOR1_WE: U31.3 (INA+)
SENSOR1_WE#: R226.1, TP30.1, U31.1 (OUTA), U31.2 (INA-)
SENSOR2_AUX: U34.5 (INB+)
SENSOR2_AUX#: R230.1, TP33.1, U34.6 (INB-), U34.7 (OUTB)
SENSOR2_WE: U34.3 (INA+)
SENSOR2_WE#: R229.1, TP32.1, U34.1 (OUTA), U34.2 (INA-)

Notes on the sheet:
QWICC SIGNAL SWITCH
VOLTAGE REFERENCE
SPS30 SIGNAL SWITCH
ALPHASENSE AFE ADC
ADC SIGNAL SWITCH (LEVEL SHIFTER)
