MIT-Senseable-City-Lab/flatburn-lte/hardware/electronics/sensors.kicad_sch

## KiCad design hardware/electronics/sensors.kicad_sch (2025-08-07)

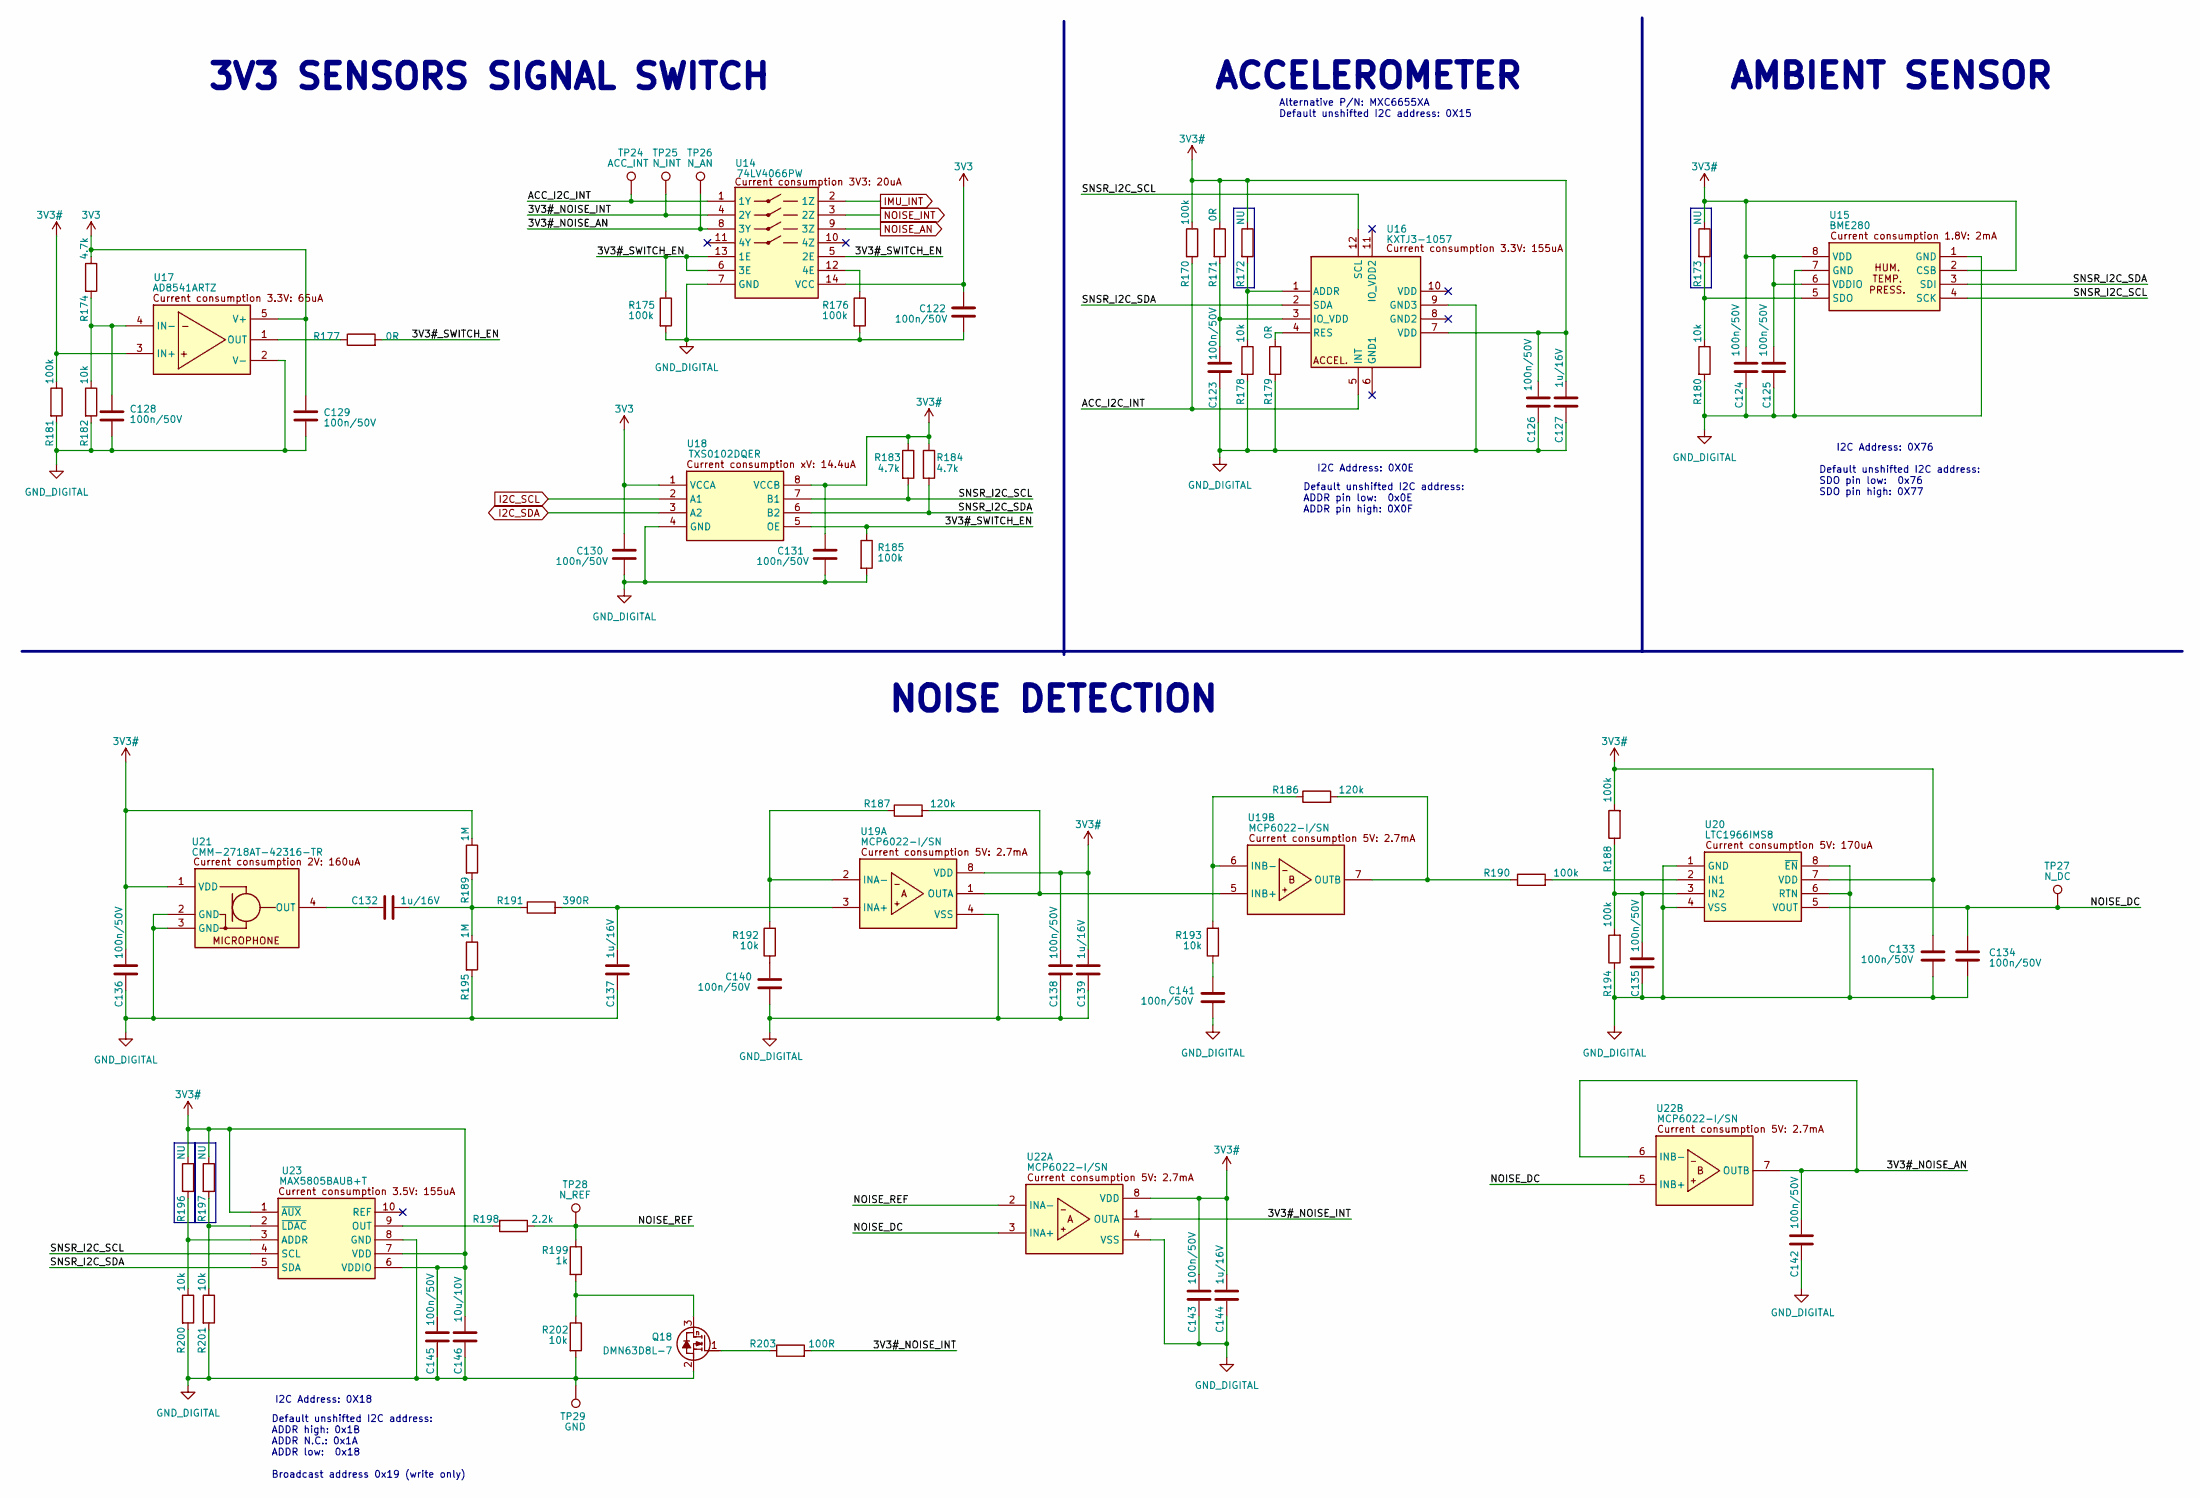
[picture p176: schematic sensors.kicad_sch]

Parts:
C122, C123, C124, C125, C126, C128, C129, C130, C131, C133, C134, C135, C136, C138, C140, C141, C142, C143, C145: 100n/50V; C_0402_1005Metric
C127, C132, C137, C139, C144: 1u/16V; C_0402_1005Metric; MPN GRM155C71C105KE11D
C146: 10u/10V; C_0603_1608Metric
Q18: DMN63D8L-7; SOT-23; MPN DMN63D8L-7
R170, R175, R176, R181, R185, R188, R190, R194: 100k; R_0402_1005Metric
R171, R177, R179: 0R; R_0402_1005Metric; MPN RCS04020000Z0ED
R172, R173, R196, R197: NU; R_0402_1005Metric
R174, R183, R184: 4.7k; R_0402_1005Metric
R178, R180, R182, R192, R193, R200, R201, R202: 10k; R_0402_1005Metric
R186, R187: 120k; R_0402_1005Metric; MPN CRCW0402120KFKED
R189, R195: 1M; R_0402_1005Metric
R191: 390R; R_0603_1608Metric
R198: 2.2k; R_0402_1005Metric
R199: 1k; R_0402_1005Metric
R203: 100R; R_0402_1005Metric
TP24: ACC_INT; TestPoint_Pad_D1.0mm
TP25: N_INT; TestPoint_Pad_D1.0mm
TP26: N_AN; TestPoint_Pad_D1.0mm
TP27: N_DC; TestPoint_Pad_D1.0mm
TP28: N_REF; TestPoint_Pad_D1.0mm
TP29: GND; TestPoint_Pad_D1.0mm
U14: 74LV4066PW; SOP65P640X110-14N; MPN 74LV4066PW,118
U15: BME280; PSON65P250X250X100-8N; MPN BME280
U16: KXTJ3-1057; LGA12_2X2X0.9_KNX-M; MPN KXTJ3-1057
U17: AD8541ARTZ; SOT-23-5; MPN TXS0102DQER
U18: TXS0102DQER; SON35P100X140X40-8N; MPN TXS0102DQER
U19, U22: MCP6022-I/SN; SOIC127P600X175-8N; MPN MCP6022-I/SN
U20: LTC1966IMS8; SOP65P490X110-8N; MPN LTC1966IMS8#PBF
U21: CMM-2718AT-42316-TR; CMM2718AT42316TR; MPN CMM-2718AT-42316-TR
U23: MAX5805BAUB+T; SOP50P490X110-10N; MPN MAX5805BAUB+T

Connections:
3V3: C122.1, C129.1, C130.1, R174.1, U14.14 (VCC), U17.5 (V+), U18.1 (VCCA)
3V3#: C124.1, C125.1, C126.1, C127.1, C131.1, C133.1, C136.1, C138.1, C139.1, C143.1, C144.1, C145.1, C146.1, R170.1, R171.1, R172.1, R173.1, R181.1, R183.1, R184.1, R188.2, R189.1, R196.1, R197.1, U15.2 (CSB), U15.6 (VDDIO), U15.8 (VDD), U16.7 (VDD), U17.3 (IN+), U18.8 (VCCB), U19.8 (VDD), U20.7 (VDD), U21.1 (VDD), U22.8 (VDD), U23.1 (~AUX), U23.6 (VDDIO), U23.7 (VDD)
3V3#_NOISE_AN: C142.1, TP26.1, U14.8 (3Y), U22.6 (INB-), U22.7 (OUTB)
3V3#_NOISE_INT: R203.2, TP25.1, U14.4 (2Y), U22.1 (OUTA)
3V3#_SWITCH_EN: R175.1, R177.2, R185.1, U14.5 (2E), U14.6 (3E), U14.13 (1E), U18.5 (OE)
ACC_I2C_INT: R170.2, TP24.1, U14.1 (1Y), U16.5 (INT)
GND_DIGITAL: C122.2, C123.2, C124.2, C125.2, C126.2, C127.2, C128.2, C129.2, C130.2, C131.2, C133.2, C134.2, C135.2, C136.2, C137.2, C138.2, C139.2, C140.2, C141.2, C142.2, C143.2, C144.2, C145.2, C146.2, Q18.2 (S), R175.2, R176.2, R178.2, R179.2, R180.2, R181.2, R182.2, R185.2, R194.1, R195.2, R200.2, R201.2, R202.2, TP29.1, U14.7 (GND), U15.1 (GND), U15.7 (GND), U16.9 (GND3), U17.2 (V-), U18.4 (GND), U19.4 (VSS), U20.1 (GND), U20.4 (VSS), U20.6 (RTN), U20.8 (~EN), U21.2 (GND), U21.3 (GND), U22.4 (VSS), U23.8 (GND)
I2C_SCL: U18.2 (A1)
I2C_SDA: U18.3 (A2)
IMU_INT: U14.2 (1Z)
NOISE_AN: U14.9 (3Z)
NOISE_DC: C134.1, TP27.1, U20.5 (VOUT), U22.3 (INA+), U22.5 (INB+)
NOISE_INT: U14.3 (2Z)
NOISE_REF: R198.1, R199.1, TP28.1, U22.2 (INA-)
unnamed: C123.1, R171.2, U16.3 (IO_VDD)
unnamed: C128.1, R174.2, R182.1, U17.4 (IN-)
unnamed: C132.1, R189.2, R191.1, R195.1
unnamed: C132.2, U21.4 (OUT)
unnamed: C135.1, R188.1, R194.2, U20.3 (IN2)
unnamed: C137.1, R191.2, U19.3 (INA+)
unnamed: C140.1, R192.1
unnamed: C141.1, R193.1
unnamed: Q18.1 (G), R203.1
unnamed: Q18.3 (D), R199.2, R202.1
unnamed: R172.2, R178.1, U16.1 (ADDR)
unnamed: R173.2, R180.1, U15.5 (SDO)
unnamed: R176.1, U14.12 (4E)
unnamed: R177.1, U17.1 (OUT)
unnamed: R179.1, U16.4 (RES)
unnamed: R186.1, R193.2, U19.6 (INB-)
unnamed: R186.2, R190.1, U19.7 (OUTB)
unnamed: R187.1, R192.2, U19.2 (INA-)
unnamed: R187.2, U19.1 (OUTA), U19.5 (INB+)
unnamed: R190.2, U20.2 (IN1)
unnamed: R196.2, R200.1, U23.3 (ADDR)
unnamed: R197.2, R201.1, U23.2 (~LDAC)
unnamed: R198.2, U23.9 (OUT)
SNSR_I2C_SCL: R183.2, U15.4 (SCK), U16.12 (SCL), U18.7 (B1), U23.4 (SCL)
SNSR_I2C_SDA: R184.2, U15.3 (SDI), U16.2 (SDA), U18.6 (B2), U23.5 (SDA)

Notes on the sheet:
3V3 SENSORS SIGNAL SWITCH
I2C Address: 0X76
ACCELEROMETER
Default unshifted I2C address: ADDR pin low: 0x0E ADDR pin high: 0X0F
AMBIENT SENSOR
Alternative P/N: MXC6655XA Default unshifted I2C address: 0X15
I2C Address: 0X18
I2C Address: 0X0E
NOISE DETECTION
Default unshifted I2C address: ADDR high: 0x1B ADDR N.C.: 0x1A ADDR low: 0x18 Broadcast address 0x19 (write only)
Default unshifted I2C address: SDO pin low: 0x76 SDO pin high: 0X77
